habakan/jitsu-in-pico/hardware/kicad/pico2h-carrier/3dprint/pico2h_case.scad

part = "assembly";
// Generated from case_dimensions.json. Units: mm.
module base() { union() {
translate([0,0,0]) linear_extrude(2.4) polygon(points=[[3.477895, 0.034221], [2.964724, 0.136297], [2.469266, 0.304482], [2.0, 0.535898], [1.564954, 0.826587], [1.171573, 1.171573], [0.826587, 1.564954], [0.535898, 2.0], [0.304482, 2.469266], [0.136297, 2.964724], [0.034221, 3.477895], [0.0, 4.0], [0.0, 39.4], [0.034221, 39.922105], [0.136297, 40.435276], [0.304482, 40.930734], [0.535898, 41.4], [0.826587, 41.835046], [1.171573, 42.228427], [1.564954, 42.573413], [2.0, 42.864102], [2.469266, 43.095518], [2.964724, 43.263703], [3.477895, 43.365779], [4.0, 43.4], [59.4, 43.4], [59.922105, 43.365779], [60.435276, 43.263703], [60.930734, 43.095518], [61.4, 42.864102], [61.835046, 42.573413], [62.228427, 42.228427], [62.573413, 41.835046], [62.864102, 41.4], [63.095518, 40.930734], [63.263703, 40.435276], [63.365779, 39.922105], [63.4, 39.4], [63.4, 4.0], [63.365779, 3.477895], [63.263703, 2.964724], [63.095518, 2.469266], [62.864102, 2.0], [62.573413, 1.564954], [62.228427, 1.171573], [61.835046, 0.826587], [61.4, 0.535898], [60.930734, 0.304482], [60.435276, 0.136297], [59.922105, 0.034221], [59.4, 0.0], [4.0, 0.0], [36.873004, 23.124736], [36.643332, 24.279371], [36.264916, 25.394151], [35.744229, 26.45], [35.09018, 27.428853], [34.313961, 28.313961], [33.428853, 29.09018], [32.45, 29.744229], [31.394151, 30.264916], [30.279371, 30.643332], [29.124736, 30.873004], [27.95, 30.95], [26.775264, 30.873004], [25.620629, 30.643332], [24.505849, 30.264916], [23.45, 29.744229], [22.471147, 29.09018], [21.586039, 28.313961], [20.80982, 27.428853], [20.155771, 26.45], [19.635084, 25.394151], [19.256668, 24.279371], [19.026996, 23.124736], [18.95, 21.95], [19.026996, 20.775264], [19.256668, 19.620629], [19.635084, 18.505849], [20.155771, 17.45], [20.80982, 16.471147], [21.586039, 15.586039], [22.471147, 14.80982], [23.45, 14.155771], [24.505849, 13.635084], [25.620629, 13.256668], [26.775264, 13.026996], [27.95, 12.95], [29.124736, 13.026996], [30.279371, 13.256668], [31.394151, 13.635084], [32.45, 14.155771], [33.428853, 14.80982], [34.313961, 15.586039], [35.09018, 16.471147], [35.744229, 17.45], [36.264916, 18.505849], [36.643332, 19.620629], [36.873004, 20.775264], [36.95, 21.95]],paths=[[0, 1, 2, 3, 4, 5, 6, 7, 8, 9, 10, 11, 12, 13, 14, 15, 16, 17, 18, 19, 20, 21, 22, 23, 24, 25, 26, 27, 28, 29, 30, 31, 32, 33, 34, 35, 36, 37, 38, 39, 40, 41, 42, 43, 44, 45, 46, 47, 48, 49, 50, 51], [52, 53, 54, 55, 56, 57, 58, 59, 60, 61, 62, 63, 64, 65, 66, 67, 68, 69, 70, 71, 72, 73, 74, 75, 76, 77, 78, 79, 80, 81, 82, 83, 84, 85, 86, 87, 88, 89, 90, 91, 92, 93, 94, 95, 96, 97, 98, 99]]);
translate([0,0,2.4]) linear_extrude(0.6000000000000001) polygon(points=[[0.034221, 39.922105], [0.136297, 40.435276], [0.304482, 40.930734], [0.535898, 41.4], [0.826587, 41.835046], [1.171573, 42.228427], [1.564954, 42.573413], [2.0, 42.864102], [2.469266, 43.095518], [2.964724, 43.263703], [3.477895, 43.365779], [4.0, 43.4], [59.4, 43.4], [59.922105, 43.365779], [60.435276, 43.263703], [60.930734, 43.095518], [61.4, 42.864102], [61.835046, 42.573413], [62.228427, 42.228427], [62.573413, 41.835046], [62.864102, 41.4], [63.095518, 40.930734], [63.263703, 40.435276], [63.365779, 39.922105], [63.4, 39.4], [63.4, 4.0], [63.365779, 3.477895], [63.263703, 2.964724], [63.095518, 2.469266], [62.864102, 2.0], [62.573413, 1.564954], [62.228427, 1.171573], [61.835046, 0.826587], [61.4, 0.535898], [60.930734, 0.304482], [60.435276, 0.136297], [59.922105, 0.034221], [59.4, 0.0], [4.0, 0.0], [3.477895, 0.034221], [2.964724, 0.136297], [2.469266, 0.304482], [2.0, 0.535898], [1.564954, 0.826587], [1.171573, 1.171573], [0.826587, 1.564954], [0.535898, 2.0], [0.304482, 2.469266], [0.136297, 2.964724], [0.034221, 3.477895], [0.0, 4.0], [0.0, 39.4], [60.817691, 3.9], [60.556072, 3.508459], [60.245584, 3.154416], [59.891541, 2.843928], [59.5, 2.582309], [59.130315, 2.4], [59.4, 2.4], [59.608842, 2.413688], [59.81411, 2.454519], [60.012293, 2.521793], [60.2, 2.614359], [60.374018, 2.730635], [60.531371, 2.868629], [60.669365, 3.025982], [60.785641, 3.2], [60.878207, 3.387707], [60.945481, 3.58589], [60.986312, 3.791158], [61.0, 4.0], [61.0, 4.269685], [59.608842, 40.986312], [59.4, 41.0], [59.130315, 41.0], [59.5, 40.817691], [59.891541, 40.556072], [60.245584, 40.245584], [60.556072, 39.891541], [60.817691, 39.5], [61.0, 39.130315], [61.0, 39.4], [60.986312, 39.608842], [60.945481, 39.81411], [60.878207, 40.012293], [60.785641, 40.2], [60.669365, 40.374018], [60.531371, 40.531371], [60.374018, 40.669365], [60.2, 40.785641], [60.012293, 40.878207], [59.81411, 40.945481], [9.3, 37.7], [9.269202, 37.230106], [9.177333, 36.768251], [9.025966, 36.32234], [8.817691, 35.9], [8.556072, 35.508459], [8.245584, 35.154416], [7.891541, 34.843928], [7.5, 34.582309], [7.07766, 34.374034], [6.631749, 34.222667], [6.169894, 34.130798], [5.7, 34.1], [5.230106, 34.130798], [4.768251, 34.222667], [4.32234, 34.374034], [3.9, 34.582309], [3.508459, 34.843928], [3.154416, 35.154416], [2.843928, 35.508459], [2.582309, 35.9], [2.4, 36.269685], [2.4, 7.130315], [2.582309, 7.5], [2.843928, 7.891541], [3.154416, 8.245584], [3.508459, 8.556072], [3.9, 8.817691], [4.32234, 9.025966], [4.768251, 9.177333], [5.230106, 9.269202], [5.7, 9.3], [6.169894, 9.269202], [6.631749, 9.177333], [7.07766, 9.025966], [7.5, 8.817691], [7.891541, 8.556072], [8.245584, 8.245584], [8.556072, 7.891541], [8.817691, 7.5], [9.025966, 7.07766], [9.177333, 6.631749], [9.269202, 6.169894], [9.3, 5.7], [9.269202, 5.230106], [9.177333, 4.768251], [9.025966, 4.32234], [8.817691, 3.9], [8.556072, 3.508459], [8.245584, 3.154416], [7.891541, 2.843928], [7.5, 2.582309], [7.130315, 2.4], [56.269685, 2.4], [55.9, 2.582309], [55.508459, 2.843928], [55.154416, 3.154416], [54.843928, 3.508459], [54.582309, 3.9], [54.374034, 4.32234], [54.222667, 4.768251], [54.130798, 5.230106], [54.1, 5.7], [54.130798, 6.169894], [54.222667, 6.631749], [54.374034, 7.07766], [54.582309, 7.5], [54.843928, 7.891541], [55.154416, 8.245584], [55.508459, 8.556072], [55.9, 8.817691], [56.32234, 9.025966], [56.768251, 9.177333], [57.230106, 9.269202], [57.7, 9.3], [58.169894, 9.269202], [58.631749, 9.177333], [59.07766, 9.025966], [59.5, 8.817691], [59.891541, 8.556072], [60.245584, 8.245584], [60.556072, 7.891541], [60.817691, 7.5], [61.0, 7.130315], [61.0, 36.269685], [60.817691, 35.9], [60.556072, 35.508459], [60.245584, 35.154416], [59.891541, 34.843928], [59.5, 34.582309], [59.07766, 34.374034], [58.631749, 34.222667], [58.169894, 34.130798], [57.7, 34.1], [57.230106, 34.130798], [56.768251, 34.222667], [56.32234, 34.374034], [55.9, 34.582309], [55.508459, 34.843928], [55.154416, 35.154416], [54.843928, 35.508459], [54.582309, 35.9], [54.374034, 36.32234], [54.222667, 36.768251], [54.130798, 37.230106], [54.1, 37.7], [54.130798, 38.169894], [54.222667, 38.631749], [54.374034, 39.07766], [54.582309, 39.5], [54.843928, 39.891541], [55.154416, 40.245584], [55.508459, 40.556072], [55.9, 40.817691], [56.269685, 41.0], [7.130315, 41.0], [7.5, 40.817691], [7.891541, 40.556072], [8.245584, 40.245584], [8.556072, 39.891541], [8.817691, 39.5], [9.025966, 39.07766], [9.177333, 38.631749], [9.269202, 38.169894], [2.454519, 39.81411], [2.413688, 39.608842], [2.4, 39.4], [2.4, 39.130315], [2.582309, 39.5], [2.843928, 39.891541], [3.154416, 40.245584], [3.508459, 40.556072], [3.9, 40.817691], [4.269685, 41.0], [4.0, 41.0], [3.791158, 40.986312], [3.58589, 40.945481], [3.387707, 40.878207], [3.2, 40.785641], [3.025982, 40.669365], [2.868629, 40.531371], [2.730635, 40.374018], [2.614359, 40.2], [2.521793, 40.012293], [4.0, 2.4], [4.269685, 2.4], [3.9, 2.582309], [3.508459, 2.843928], [3.154416, 3.154416], [2.843928, 3.508459], [2.582309, 3.9], [2.4, 4.269685], [2.4, 4.0], [2.413688, 3.791158], [2.454519, 3.58589], [2.521793, 3.387707], [2.614359, 3.2], [2.730635, 3.025982], [2.868629, 2.868629], [3.025982, 2.730635], [3.2, 2.614359], [3.387707, 2.521793], [3.58589, 2.454519], [3.791158, 2.413688]],paths=[[0, 1, 2, 3, 4, 5, 6, 7, 8, 9, 10, 11, 12, 13, 14, 15, 16, 17, 18, 19, 20, 21, 22, 23, 24, 25, 26, 27, 28, 29, 30, 31, 32, 33, 34, 35, 36, 37, 38, 39, 40, 41, 42, 43, 44, 45, 46, 47, 48, 49, 50, 51], [52, 53, 54, 55, 56, 57, 58, 59, 60, 61, 62, 63, 64, 65, 66, 67, 68, 69, 70, 71], [72, 73, 74, 75, 76, 77, 78, 79, 80, 81, 82, 83, 84, 85, 86, 87, 88, 89, 90, 91], [92, 93, 94, 95, 96, 97, 98, 99, 100, 101, 102, 103, 104, 105, 106, 107, 108, 109, 110, 111, 112, 113, 114, 115, 116, 117, 118, 119, 120, 121, 122, 123, 124, 125, 126, 127, 128, 129, 130, 131, 132, 133, 134, 135, 136, 137, 138, 139, 140, 141, 142, 143, 144, 145, 146, 147, 148, 149, 150, 151, 152, 153, 154, 155, 156, 157, 158, 159, 160, 161, 162, 163, 164, 165, 166, 167, 168, 169, 170, 171, 172, 173, 174, 175, 176, 177, 178, 179, 180, 181, 182, 183, 184, 185, 186, 187, 188, 189, 190, 191, 192, 193, 194, 195, 196, 197, 198, 199, 200, 201, 202, 203, 204, 205, 206, 207, 208, 209, 210, 211, 212, 213, 214, 215], [216, 217, 218, 219, 220, 221, 222, 223, 224, 225, 226, 227, 228, 229, 230, 231, 232, 233, 234, 235], [236, 237, 238, 239, 240, 241, 242, 243, 244, 245, 246, 247, 248, 249, 250, 251, 252, 253, 254, 255]]);
translate([0,0,2.4]) linear_extrude(0.6000000000000001) polygon(points=[[10.8, 12.794744], [10.541904, 12.667465], [10.269402, 12.574963], [9.987158, 12.518821], [9.7, 12.5], [9.412842, 12.518821], [9.130598, 12.574963], [8.858096, 12.667465], [8.6, 12.794744], [8.360725, 12.954623], [8.144365, 13.144365], [7.954623, 13.360725], [7.794744, 13.6], [7.667465, 13.858096], [7.574963, 14.130598], [7.518821, 14.412842], [7.5, 14.7], [7.518821, 14.987158], [7.574963, 15.269402], [7.667465, 15.541904], [7.794744, 15.8], [7.954623, 16.039275], [8.144365, 16.255635], [8.360725, 16.445377], [8.6, 16.605256], [8.858096, 16.732535], [9.130598, 16.825037], [9.412842, 16.881179], [9.7, 16.9], [9.987158, 16.881179], [10.269402, 16.825037], [10.541904, 16.732535], [10.8, 16.605256], [11.039275, 16.445377], [11.255635, 16.255635], [11.445377, 16.039275], [11.605256, 15.8], [11.732535, 15.541904], [11.825037, 15.269402], [11.881179, 14.987158], [11.9, 14.7], [11.881179, 14.412842], [11.825037, 14.130598], [11.732535, 13.858096], [11.605256, 13.6], [11.445377, 13.360725], [11.255635, 13.144365], [11.039275, 12.954623]],paths=[[0, 1, 2, 3, 4, 5, 6, 7, 8, 9, 10, 11, 12, 13, 14, 15, 16, 17, 18, 19, 20, 21, 22, 23, 24, 25, 26, 27, 28, 29, 30, 31, 32, 33, 34, 35, 36, 37, 38, 39, 40, 41, 42, 43, 44, 45, 46, 47]]);
translate([0,0,2.4]) linear_extrude(0.6000000000000001) polygon(points=[[11.039275, 27.454623], [10.8, 27.294744], [10.541904, 27.167465], [10.269402, 27.074963], [9.987158, 27.018821], [9.7, 27.0], [9.412842, 27.018821], [9.130598, 27.074963], [8.858096, 27.167465], [8.6, 27.294744], [8.360725, 27.454623], [8.144365, 27.644365], [7.954623, 27.860725], [7.794744, 28.1], [7.667465, 28.358096], [7.574963, 28.630598], [7.518821, 28.912842], [7.5, 29.2], [7.518821, 29.487158], [7.574963, 29.769402], [7.667465, 30.041904], [7.794744, 30.3], [7.954623, 30.539275], [8.144365, 30.755635], [8.360725, 30.945377], [8.6, 31.105256], [8.858096, 31.232535], [9.130598, 31.325037], [9.412842, 31.381179], [9.7, 31.4], [9.987158, 31.381179], [10.269402, 31.325037], [10.541904, 31.232535], [10.8, 31.105256], [11.039275, 30.945377], [11.255635, 30.755635], [11.445377, 30.539275], [11.605256, 30.3], [11.732535, 30.041904], [11.825037, 29.769402], [11.881179, 29.487158], [11.9, 29.2], [11.881179, 28.912842], [11.825037, 28.630598], [11.732535, 28.358096], [11.605256, 28.1], [11.445377, 27.860725], [11.255635, 27.644365]],paths=[[0, 1, 2, 3, 4, 5, 6, 7, 8, 9, 10, 11, 12, 13, 14, 15, 16, 17, 18, 19, 20, 21, 22, 23, 24, 25, 26, 27, 28, 29, 30, 31, 32, 33, 34, 35, 36, 37, 38, 39, 40, 41, 42, 43, 44, 45, 46, 47]]);
translate([0,0,2.4]) linear_extrude(0.6000000000000001) polygon(points=[[47.755635, 13.144365], [47.539275, 12.954623], [47.3, 12.794744], [47.041904, 12.667465], [46.769402, 12.574963], [46.487158, 12.518821], [46.2, 12.5], [45.912842, 12.518821], [45.630598, 12.574963], [45.358096, 12.667465], [45.1, 12.794744], [44.860725, 12.954623], [44.644365, 13.144365], [44.454623, 13.360725], [44.294744, 13.6], [44.167465, 13.858096], [44.074963, 14.130598], [44.018821, 14.412842], [44.0, 14.7], [44.018821, 14.987158], [44.074963, 15.269402], [44.167465, 15.541904], [44.294744, 15.8], [44.454623, 16.039275], [44.644365, 16.255635], [44.860725, 16.445377], [45.1, 16.605256], [45.358096, 16.732535], [45.630598, 16.825037], [45.912842, 16.881179], [46.2, 16.9], [46.487158, 16.881179], [46.769402, 16.825037], [47.041904, 16.732535], [47.3, 16.605256], [47.539275, 16.445377], [47.755635, 16.255635], [47.945377, 16.039275], [48.105256, 15.8], [48.232535, 15.541904], [48.325037, 15.269402], [48.381179, 14.987158], [48.4, 14.7], [48.381179, 14.412842], [48.325037, 14.130598], [48.232535, 13.858096], [48.105256, 13.6], [47.945377, 13.360725]],paths=[[0, 1, 2, 3, 4, 5, 6, 7, 8, 9, 10, 11, 12, 13, 14, 15, 16, 17, 18, 19, 20, 21, 22, 23, 24, 25, 26, 27, 28, 29, 30, 31, 32, 33, 34, 35, 36, 37, 38, 39, 40, 41, 42, 43, 44, 45, 46, 47]]);
translate([0,0,2.4]) linear_extrude(0.6000000000000001) polygon(points=[[47.945377, 27.860725], [47.755635, 27.644365], [47.539275, 27.454623], [47.3, 27.294744], [47.041904, 27.167465], [46.769402, 27.074963], [46.487158, 27.018821], [46.2, 27.0], [45.912842, 27.018821], [45.630598, 27.074963], [45.358096, 27.167465], [45.1, 27.294744], [44.860725, 27.454623], [44.644365, 27.644365], [44.454623, 27.860725], [44.294744, 28.1], [44.167465, 28.358096], [44.074963, 28.630598], [44.018821, 28.912842], [44.0, 29.2], [44.018821, 29.487158], [44.074963, 29.769402], [44.167465, 30.041904], [44.294744, 30.3], [44.454623, 30.539275], [44.644365, 30.755635], [44.860725, 30.945377], [45.1, 31.105256], [45.358096, 31.232535], [45.630598, 31.325037], [45.912842, 31.381179], [46.2, 31.4], [46.487158, 31.381179], [46.769402, 31.325037], [47.041904, 31.232535], [47.3, 31.105256], [47.539275, 30.945377], [47.755635, 30.755635], [47.945377, 30.539275], [48.105256, 30.3], [48.232535, 30.041904], [48.325037, 29.769402], [48.381179, 29.487158], [48.4, 29.2], [48.381179, 28.912842], [48.325037, 28.630598], [48.232535, 28.358096], [48.105256, 28.1]],paths=[[0, 1, 2, 3, 4, 5, 6, 7, 8, 9, 10, 11, 12, 13, 14, 15, 16, 17, 18, 19, 20, 21, 22, 23, 24, 25, 26, 27, 28, 29, 30, 31, 32, 33, 34, 35, 36, 37, 38, 39, 40, 41, 42, 43, 44, 45, 46, 47]]);
translate([0,0,2.4]) linear_extrude(0.6000000000000001) polygon(points=[[13.9, 6.7], [12.7, 6.7], [12.7, 7.9], [13.9, 7.9]],paths=[[0, 1, 2, 3]]);
translate([0,0,2.4]) linear_extrude(0.6000000000000001) polygon(points=[[13.9, 37.2], [13.9, 36.0], [12.7, 36.0], [12.7, 37.2]],paths=[[0, 1, 2, 3]]);
translate([0,0,2.4]) linear_extrude(0.6000000000000001) polygon(points=[[42.0, 7.9], [43.2, 7.9], [43.2, 6.7], [42.0, 6.7]],paths=[[0, 1, 2, 3]]);
translate([0,0,2.4]) linear_extrude(0.6000000000000001) polygon(points=[[42.0, 36.0], [42.0, 37.2], [43.2, 37.2], [43.2, 36.0]],paths=[[0, 1, 2, 3]]);
translate([0,0,3.0]) linear_extrude(0.3999999999999999) polygon(points=[[0.826587, 41.835046], [1.171573, 42.228427], [1.564954, 42.573413], [2.0, 42.864102], [2.469266, 43.095518], [2.964724, 43.263703], [3.477895, 43.365779], [4.0, 43.4], [59.4, 43.4], [59.922105, 43.365779], [60.435276, 43.263703], [60.930734, 43.095518], [61.4, 42.864102], [61.835046, 42.573413], [62.228427, 42.228427], [62.573413, 41.835046], [62.864102, 41.4], [63.095518, 40.930734], [63.263703, 40.435276], [63.365779, 39.922105], [63.4, 39.4], [63.4, 4.0], [63.365779, 3.477895], [63.263703, 2.964724], [63.095518, 2.469266], [62.864102, 2.0], [62.573413, 1.564954], [62.228427, 1.171573], [61.835046, 0.826587], [61.4, 0.535898], [60.930734, 0.304482], [60.435276, 0.136297], [59.922105, 0.034221], [59.4, 0.0], [4.0, 0.0], [3.477895, 0.034221], [2.964724, 0.136297], [2.469266, 0.304482], [2.0, 0.535898], [1.564954, 0.826587], [1.171573, 1.171573], [0.826587, 1.564954], [0.535898, 2.0], [0.304482, 2.469266], [0.136297, 2.964724], [0.034221, 3.477895], [0.0, 4.0], [0.0, 39.4], [0.034221, 39.922105], [0.136297, 40.435276], [0.304482, 40.930734], [0.535898, 41.4], [59.5, 2.582309], [59.130315, 2.4], [59.4, 2.4], [59.608842, 2.413688], [59.81411, 2.454519], [60.012293, 2.521793], [60.2, 2.614359], [60.374018, 2.730635], [60.531371, 2.868629], [60.669365, 3.025982], [60.785641, 3.2], [60.878207, 3.387707], [60.945481, 3.58589], [60.986312, 3.791158], [61.0, 4.0], [61.0, 4.269685], [60.817691, 3.9], [60.556072, 3.508459], [60.245584, 3.154416], [59.891541, 2.843928], [59.891541, 40.556072], [60.245584, 40.245584], [60.556072, 39.891541], [60.817691, 39.5], [61.0, 39.130315], [61.0, 39.4], [60.986312, 39.608842], [60.945481, 39.81411], [60.878207, 40.012293], [60.785641, 40.2], [60.669365, 40.374018], [60.531371, 40.531371], [60.374018, 40.669365], [60.2, 40.785641], [60.012293, 40.878207], [59.81411, 40.945481], [59.608842, 40.986312], [59.4, 41.0], [59.130315, 41.0], [59.5, 40.817691], [8.817691, 35.9], [8.556072, 35.508459], [8.245584, 35.154416], [7.891541, 34.843928], [7.5, 34.582309], [7.07766, 34.374034], [6.631749, 34.222667], [6.169894, 34.130798], [5.7, 34.1], [5.230106, 34.130798], [4.768251, 34.222667], [4.32234, 34.374034], [3.9, 34.582309], [3.508459, 34.843928], [3.154416, 35.154416], [2.843928, 35.508459], [2.582309, 35.9], [2.4, 36.269685], [2.4, 7.130315], [2.582309, 7.5], [2.843928, 7.891541], [3.154416, 8.245584], [3.508459, 8.556072], [3.9, 8.817691], [4.32234, 9.025966], [4.768251, 9.177333], [5.230106, 9.269202], [5.7, 9.3], [6.169894, 9.269202], [6.631749, 9.177333], [7.07766, 9.025966], [7.5, 8.817691], [7.891541, 8.556072], [8.245584, 8.245584], [8.556072, 7.891541], [8.817691, 7.5], [9.025966, 7.07766], [9.177333, 6.631749], [9.269202, 6.169894], [9.3, 5.7], [9.269202, 5.230106], [9.177333, 4.768251], [9.025966, 4.32234], [8.817691, 3.9], [8.556072, 3.508459], [8.245584, 3.154416], [7.891541, 2.843928], [7.5, 2.582309], [7.130315, 2.4], [56.269685, 2.4], [55.9, 2.582309], [55.508459, 2.843928], [55.154416, 3.154416], [54.843928, 3.508459], [54.582309, 3.9], [54.374034, 4.32234], [54.222667, 4.768251], [54.130798, 5.230106], [54.1, 5.7], [54.130798, 6.169894], [54.222667, 6.631749], [54.374034, 7.07766], [54.582309, 7.5], [54.843928, 7.891541], [55.154416, 8.245584], [55.508459, 8.556072], [55.9, 8.817691], [56.32234, 9.025966], [56.768251, 9.177333], [57.230106, 9.269202], [57.7, 9.3], [58.169894, 9.269202], [58.631749, 9.177333], [59.07766, 9.025966], [59.5, 8.817691], [59.891541, 8.556072], [60.245584, 8.245584], [60.556072, 7.891541], [60.817691, 7.5], [61.0, 7.130315], [61.0, 36.269685], [60.817691, 35.9], [60.556072, 35.508459], [60.245584, 35.154416], [59.891541, 34.843928], [59.5, 34.582309], [59.07766, 34.374034], [58.631749, 34.222667], [58.169894, 34.130798], [57.7, 34.1], [57.230106, 34.130798], [56.768251, 34.222667], [56.32234, 34.374034], [55.9, 34.582309], [55.508459, 34.843928], [55.154416, 35.154416], [54.843928, 35.508459], [54.582309, 35.9], [54.374034, 36.32234], [54.222667, 36.768251], [54.130798, 37.230106], [54.1, 37.7], [54.130798, 38.169894], [54.222667, 38.631749], [54.374034, 39.07766], [54.582309, 39.5], [54.843928, 39.891541], [55.154416, 40.245584], [55.508459, 40.556072], [55.9, 40.817691], [56.269685, 41.0], [7.130315, 41.0], [7.5, 40.817691], [7.891541, 40.556072], [8.245584, 40.245584], [8.556072, 39.891541], [8.817691, 39.5], [9.025966, 39.07766], [9.177333, 38.631749], [9.269202, 38.169894], [9.3, 37.7], [9.269202, 37.230106], [9.177333, 36.768251], [9.025966, 36.32234], [2.582309, 39.5], [2.843928, 39.891541], [3.154416, 40.245584], [3.508459, 40.556072], [3.9, 40.817691], [4.269685, 41.0], [4.0, 41.0], [3.791158, 40.986312], [3.58589, 40.945481], [3.387707, 40.878207], [3.2, 40.785641], [3.025982, 40.669365], [2.868629, 40.531371], [2.730635, 40.374018], [2.614359, 40.2], [2.521793, 40.012293], [2.454519, 39.81411], [2.413688, 39.608842], [2.4, 39.4], [2.4, 39.130315], [3.154416, 3.154416], [2.843928, 3.508459], [2.582309, 3.9], [2.4, 4.269685], [2.4, 4.0], [2.413688, 3.791158], [2.454519, 3.58589], [2.521793, 3.387707], [2.614359, 3.2], [2.730635, 3.025982], [2.868629, 2.868629], [3.025982, 2.730635], [3.2, 2.614359], [3.387707, 2.521793], [3.58589, 2.454519], [3.791158, 2.413688], [4.0, 2.4], [4.269685, 2.4], [3.9, 2.582309], [3.508459, 2.843928]],paths=[[0, 1, 2, 3, 4, 5, 6, 7, 8, 9, 10, 11, 12, 13, 14, 15, 16, 17, 18, 19, 20, 21, 22, 23, 24, 25, 26, 27, 28, 29, 30, 31, 32, 33, 34, 35, 36, 37, 38, 39, 40, 41, 42, 43, 44, 45, 46, 47, 48, 49, 50, 51], [52, 53, 54, 55, 56, 57, 58, 59, 60, 61, 62, 63, 64, 65, 66, 67, 68, 69, 70, 71], [72, 73, 74, 75, 76, 77, 78, 79, 80, 81, 82, 83, 84, 85, 86, 87, 88, 89, 90, 91], [92, 93, 94, 95, 96, 97, 98, 99, 100, 101, 102, 103, 104, 105, 106, 107, 108, 109, 110, 111, 112, 113, 114, 115, 116, 117, 118, 119, 120, 121, 122, 123, 124, 125, 126, 127, 128, 129, 130, 131, 132, 133, 134, 135, 136, 137, 138, 139, 140, 141, 142, 143, 144, 145, 146, 147, 148, 149, 150, 151, 152, 153, 154, 155, 156, 157, 158, 159, 160, 161, 162, 163, 164, 165, 166, 167, 168, 169, 170, 171, 172, 173, 174, 175, 176, 177, 178, 179, 180, 181, 182, 183, 184, 185, 186, 187, 188, 189, 190, 191, 192, 193, 194, 195, 196, 197, 198, 199, 200, 201, 202, 203, 204, 205, 206, 207, 208, 209, 210, 211, 212, 213, 214, 215], [216, 217, 218, 219, 220, 221, 222, 223, 224, 225, 226, 227, 228, 229, 230, 231, 232, 233, 234, 235], [236, 237, 238, 239, 240, 241, 242, 243, 244, 245, 246, 247, 248, 249, 250, 251, 252, 253, 254, 255]]);
translate([0,0,3.0]) linear_extrude(0.3999999999999999) polygon(points=[[9.7, 12.5], [9.412842, 12.518821], [9.130598, 12.574963], [8.858096, 12.667465], [8.6, 12.794744], [8.360725, 12.954623], [8.144365, 13.144365], [7.954623, 13.360725], [7.794744, 13.6], [7.667465, 13.858096], [7.574963, 14.130598], [7.518821, 14.412842], [7.5, 14.7], [7.518821, 14.987158], [7.574963, 15.269402], [7.667465, 15.541904], [7.794744, 15.8], [7.954623, 16.039275], [8.144365, 16.255635], [8.360725, 16.445377], [8.6, 16.605256], [8.858096, 16.732535], [9.130598, 16.825037], [9.412842, 16.881179], [9.7, 16.9], [9.987158, 16.881179], [10.269402, 16.825037], [10.541904, 16.732535], [10.8, 16.605256], [11.039275, 16.445377], [11.255635, 16.255635], [11.445377, 16.039275], [11.605256, 15.8], [11.732535, 15.541904], [11.825037, 15.269402], [11.881179, 14.987158], [11.9, 14.7], [11.881179, 14.412842], [11.825037, 14.130598], [11.732535, 13.858096], [11.605256, 13.6], [11.445377, 13.360725], [11.255635, 13.144365], [11.039275, 12.954623], [10.8, 12.794744], [10.541904, 12.667465], [10.269402, 12.574963], [9.987158, 12.518821], [9.804421, 15.493156], [9.7, 15.5], [9.595579, 15.493156], [9.492945, 15.472741], [9.393853, 15.439104], [9.3, 15.39282], [9.212991, 15.334683], [9.134315, 15.265685], [9.065317, 15.187009], [9.00718, 15.1], [8.960896, 15.006147], [8.927259, 14.907055], [8.906844, 14.804421], [8.9, 14.7], [8.906844, 14.595579], [8.927259, 14.492945], [8.960896, 14.393853], [9.00718, 14.3], [9.065317, 14.212991], [9.134315, 14.134315], [9.212991, 14.065317], [9.3, 14.00718], [9.393853, 13.960896], [9.492945, 13.927259], [9.595579, 13.906844], [9.7, 13.9], [9.804421, 13.906844], [9.907055, 13.927259], [10.006147, 13.960896], [10.1, 14.00718], [10.187009, 14.065317], [10.265685, 14.134315], [10.334683, 14.212991], [10.39282, 14.3], [10.439104, 14.393853], [10.472741, 14.492945], [10.493156, 14.595579], [10.5, 14.7], [10.493156, 14.804421], [10.472741, 14.907055], [10.439104, 15.006147], [10.39282, 15.1], [10.334683, 15.187009], [10.265685, 15.265685], [10.187009, 15.334683], [10.1, 15.39282], [10.006147, 15.439104], [9.907055, 15.472741]],paths=[[0, 1, 2, 3, 4, 5, 6, 7, 8, 9, 10, 11, 12, 13, 14, 15, 16, 17, 18, 19, 20, 21, 22, 23, 24, 25, 26, 27, 28, 29, 30, 31, 32, 33, 34, 35, 36, 37, 38, 39, 40, 41, 42, 43, 44, 45, 46, 47], [48, 49, 50, 51, 52, 53, 54, 55, 56, 57, 58, 59, 60, 61, 62, 63, 64, 65, 66, 67, 68, 69, 70, 71, 72, 73, 74, 75, 76, 77, 78, 79, 80, 81, 82, 83, 84, 85, 86, 87, 88, 89, 90, 91, 92, 93, 94, 95]]);
translate([0,0,3.0]) linear_extrude(0.3999999999999999) polygon(points=[[10.269402, 27.074963], [9.987158, 27.018821], [9.7, 27.0], [9.412842, 27.018821], [9.130598, 27.074963], [8.858096, 27.167465], [8.6, 27.294744], [8.360725, 27.454623], [8.144365, 27.644365], [7.954623, 27.860725], [7.794744, 28.1], [7.667465, 28.358096], [7.574963, 28.630598], [7.518821, 28.912842], [7.5, 29.2], [7.518821, 29.487158], [7.574963, 29.769402], [7.667465, 30.041904], [7.794744, 30.3], [7.954623, 30.539275], [8.144365, 30.755635], [8.360725, 30.945377], [8.6, 31.105256], [8.858096, 31.232535], [9.130598, 31.325037], [9.412842, 31.381179], [9.7, 31.4], [9.987158, 31.381179], [10.269402, 31.325037], [10.541904, 31.232535], [10.8, 31.105256], [11.039275, 30.945377], [11.255635, 30.755635], [11.445377, 30.539275], [11.605256, 30.3], [11.732535, 30.041904], [11.825037, 29.769402], [11.881179, 29.487158], [11.9, 29.2], [11.881179, 28.912842], [11.825037, 28.630598], [11.732535, 28.358096], [11.605256, 28.1], [11.445377, 27.860725], [11.255635, 27.644365], [11.039275, 27.454623], [10.8, 27.294744], [10.541904, 27.167465], [10.006147, 29.939104], [9.907055, 29.972741], [9.804421, 29.993156], [9.7, 30.0], [9.595579, 29.993156], [9.492945, 29.972741], [9.393853, 29.939104], [9.3, 29.89282], [9.212991, 29.834683], [9.134315, 29.765685], [9.065317, 29.687009], [9.00718, 29.6], [8.960896, 29.506147], [8.927259, 29.407055], [8.906844, 29.304421], [8.9, 29.2], [8.906844, 29.095579], [8.927259, 28.992945], [8.960896, 28.893853], [9.00718, 28.8], [9.065317, 28.712991], [9.134315, 28.634315], [9.212991, 28.565317], [9.3, 28.50718], [9.393853, 28.460896], [9.492945, 28.427259], [9.595579, 28.406844], [9.7, 28.4], [9.804421, 28.406844], [9.907055, 28.427259], [10.006147, 28.460896], [10.1, 28.50718], [10.187009, 28.565317], [10.265685, 28.634315], [10.334683, 28.712991], [10.39282, 28.8], [10.439104, 28.893853], [10.472741, 28.992945], [10.493156, 29.095579], [10.5, 29.2], [10.493156, 29.304421], [10.472741, 29.407055], [10.439104, 29.506147], [10.39282, 29.6], [10.334683, 29.687009], [10.265685, 29.765685], [10.187009, 29.834683], [10.1, 29.89282]],paths=[[0, 1, 2, 3, 4, 5, 6, 7, 8, 9, 10, 11, 12, 13, 14, 15, 16, 17, 18, 19, 20, 21, 22, 23, 24, 25, 26, 27, 28, 29, 30, 31, 32, 33, 34, 35, 36, 37, 38, 39, 40, 41, 42, 43, 44, 45, 46, 47], [48, 49, 50, 51, 52, 53, 54, 55, 56, 57, 58, 59, 60, 61, 62, 63, 64, 65, 66, 67, 68, 69, 70, 71, 72, 73, 74, 75, 76, 77, 78, 79, 80, 81, 82, 83, 84, 85, 86, 87, 88, 89, 90, 91, 92, 93, 94, 95]]);
translate([0,0,3.0]) linear_extrude(0.3999999999999999) polygon(points=[[47.3, 12.794744], [47.041904, 12.667465], [46.769402, 12.574963], [46.487158, 12.518821], [46.2, 12.5], [45.912842, 12.518821], [45.630598, 12.574963], [45.358096, 12.667465], [45.1, 12.794744], [44.860725, 12.954623], [44.644365, 13.144365], [44.454623, 13.360725], [44.294744, 13.6], [44.167465, 13.858096], [44.074963, 14.130598], [44.018821, 14.412842], [44.0, 14.7], [44.018821, 14.987158], [44.074963, 15.269402], [44.167465, 15.541904], [44.294744, 15.8], [44.454623, 16.039275], [44.644365, 16.255635], [44.860725, 16.445377], [45.1, 16.605256], [45.358096, 16.732535], [45.630598, 16.825037], [45.912842, 16.881179], [46.2, 16.9], [46.487158, 16.881179], [46.769402, 16.825037], [47.041904, 16.732535], [47.3, 16.605256], [47.539275, 16.445377], [47.755635, 16.255635], [47.945377, 16.039275], [48.105256, 15.8], [48.232535, 15.541904], [48.325037, 15.269402], [48.381179, 14.987158], [48.4, 14.7], [48.381179, 14.412842], [48.325037, 14.130598], [48.232535, 13.858096], [48.105256, 13.6], [47.945377, 13.360725], [47.755635, 13.144365], [47.539275, 12.954623], [46.687009, 15.334683], [46.6, 15.39282], [46.506147, 15.439104], [46.407055, 15.472741], [46.304421, 15.493156], [46.2, 15.5], [46.095579, 15.493156], [45.992945, 15.472741], [45.893853, 15.439104], [45.8, 15.39282], [45.712991, 15.334683], [45.634315, 15.265685], [45.565317, 15.187009], [45.50718, 15.1], [45.460896, 15.006147], [45.427259, 14.907055], [45.406844, 14.804421], [45.4, 14.7], [45.406844, 14.595579], [45.427259, 14.492945], [45.460896, 14.393853], [45.50718, 14.3], [45.565317, 14.212991], [45.634315, 14.134315], [45.712991, 14.065317], [45.8, 14.00718], [45.893853, 13.960896], [45.992945, 13.927259], [46.095579, 13.906844], [46.2, 13.9], [46.304421, 13.906844], [46.407055, 13.927259], [46.506147, 13.960896], [46.6, 14.00718], [46.687009, 14.065317], [46.765685, 14.134315], [46.834683, 14.212991], [46.89282, 14.3], [46.939104, 14.393853], [46.972741, 14.492945], [46.993156, 14.595579], [47.0, 14.7], [46.993156, 14.804421], [46.972741, 14.907055], [46.939104, 15.006147], [46.89282, 15.1], [46.834683, 15.187009], [46.765685, 15.265685]],paths=[[0, 1, 2, 3, 4, 5, 6, 7, 8, 9, 10, 11, 12, 13, 14, 15, 16, 17, 18, 19, 20, 21, 22, 23, 24, 25, 26, 27, 28, 29, 30, 31, 32, 33, 34, 35, 36, 37, 38, 39, 40, 41, 42, 43, 44, 45, 46, 47], [48, 49, 50, 51, 52, 53, 54, 55, 56, 57, 58, 59, 60, 61, 62, 63, 64, 65, 66, 67, 68, 69, 70, 71, 72, 73, 74, 75, 76, 77, 78, 79, 80, 81, 82, 83, 84, 85, 86, 87, 88, 89, 90, 91, 92, 93, 94, 95]]);
translate([0,0,3.0]) linear_extrude(0.3999999999999999) polygon(points=[[47.755635, 27.644365], [47.539275, 27.454623], [47.3, 27.294744], [47.041904, 27.167465], [46.769402, 27.074963], [46.487158, 27.018821], [46.2, 27.0], [45.912842, 27.018821], [45.630598, 27.074963], [45.358096, 27.167465], [45.1, 27.294744], [44.860725, 27.454623], [44.644365, 27.644365], [44.454623, 27.860725], [44.294744, 28.1], [44.167465, 28.358096], [44.074963, 28.630598], [44.018821, 28.912842], [44.0, 29.2], [44.018821, 29.487158], [44.074963, 29.769402], [44.167465, 30.041904], [44.294744, 30.3], [44.454623, 30.539275], [44.644365, 30.755635], [44.860725, 30.945377], [45.1, 31.105256], [45.358096, 31.232535], [45.630598, 31.325037], [45.912842, 31.381179], [46.2, 31.4], [46.487158, 31.381179], [46.769402, 31.325037], [47.041904, 31.232535], [47.3, 31.105256], [47.539275, 30.945377], [47.755635, 30.755635], [47.945377, 30.539275], [48.105256, 30.3], [48.232535, 30.041904], [48.325037, 29.769402], [48.381179, 29.487158], [48.4, 29.2], [48.381179, 28.912842], [48.325037, 28.630598], [48.232535, 28.358096], [48.105256, 28.1], [47.945377, 27.860725], [46.834683, 29.687009], [46.765685, 29.765685], [46.687009, 29.834683], [46.6, 29.89282], [46.506147, 29.939104], [46.407055, 29.972741], [46.304421, 29.993156], [46.2, 30.0], [46.095579, 29.993156], [45.992945, 29.972741], [45.893853, 29.939104], [45.8, 29.89282], [45.712991, 29.834683], [45.634315, 29.765685], [45.565317, 29.687009], [45.50718, 29.6], [45.460896, 29.506147], [45.427259, 29.407055], [45.406844, 29.304421], [45.4, 29.2], [45.406844, 29.095579], [45.427259, 28.992945], [45.460896, 28.893853], [45.50718, 28.8], [45.565317, 28.712991], [45.634315, 28.634315], [45.712991, 28.565317], [45.8, 28.50718], [45.893853, 28.460896], [45.992945, 28.427259], [46.095579, 28.406844], [46.2, 28.4], [46.304421, 28.406844], [46.407055, 28.427259], [46.506147, 28.460896], [46.6, 28.50718], [46.687009, 28.565317], [46.765685, 28.634315], [46.834683, 28.712991], [46.89282, 28.8], [46.939104, 28.893853], [46.972741, 28.992945], [46.993156, 29.095579], [47.0, 29.2], [46.993156, 29.304421], [46.972741, 29.407055], [46.939104, 29.506147], [46.89282, 29.6]],paths=[[0, 1, 2, 3, 4, 5, 6, 7, 8, 9, 10, 11, 12, 13, 14, 15, 16, 17, 18, 19, 20, 21, 22, 23, 24, 25, 26, 27, 28, 29, 30, 31, 32, 33, 34, 35, 36, 37, 38, 39, 40, 41, 42, 43, 44, 45, 46, 47], [48, 49, 50, 51, 52, 53, 54, 55, 56, 57, 58, 59, 60, 61, 62, 63, 64, 65, 66, 67, 68, 69, 70, 71, 72, 73, 74, 75, 76, 77, 78, 79, 80, 81, 82, 83, 84, 85, 86, 87, 88, 89, 90, 91, 92, 93, 94, 95]]);
translate([0,0,3.0]) linear_extrude(0.3999999999999999) polygon(points=[[13.9, 6.7], [12.7, 6.7], [12.7, 7.9], [13.9, 7.9]],paths=[[0, 1, 2, 3]]);
translate([0,0,3.0]) linear_extrude(0.3999999999999999) polygon(points=[[13.9, 37.2], [13.9, 36.0], [12.7, 36.0], [12.7, 37.2]],paths=[[0, 1, 2, 3]]);
translate([0,0,3.0]) linear_extrude(0.3999999999999999) polygon(points=[[42.0, 7.9], [43.2, 7.9], [43.2, 6.7], [42.0, 6.7]],paths=[[0, 1, 2, 3]]);
translate([0,0,3.0]) linear_extrude(0.3999999999999999) polygon(points=[[42.0, 36.0], [42.0, 37.2], [43.2, 37.2], [43.2, 36.0]],paths=[[0, 1, 2, 3]]);
translate([0,0,3.4]) linear_extrude(0.8000000000000003) polygon(points=[[0.535898, 41.4], [0.826587, 41.835046], [1.171573, 42.228427], [1.564954, 42.573413], [2.0, 42.864102], [2.469266, 43.095518], [2.964724, 43.263703], [3.477895, 43.365779], [4.0, 43.4], [59.4, 43.4], [59.922105, 43.365779], [60.435276, 43.263703], [60.930734, 43.095518], [61.4, 42.864102], [61.835046, 42.573413], [62.228427, 42.228427], [62.573413, 41.835046], [62.864102, 41.4], [63.095518, 40.930734], [63.263703, 40.435276], [63.365779, 39.922105], [63.4, 39.4], [63.4, 4.0], [63.365779, 3.477895], [63.263703, 2.964724], [63.095518, 2.469266], [62.864102, 2.0], [62.573413, 1.564954], [62.228427, 1.171573], [61.835046, 0.826587], [61.4, 0.535898], [60.930734, 0.304482], [60.435276, 0.136297], [59.922105, 0.034221], [59.4, 0.0], [4.0, 0.0], [3.477895, 0.034221], [2.964724, 0.136297], [2.469266, 0.304482], [2.0, 0.535898], [1.564954, 0.826587], [1.171573, 1.171573], [0.826587, 1.564954], [0.535898, 2.0], [0.304482, 2.469266], [0.136297, 2.964724], [0.034221, 3.477895], [0.0, 4.0], [0.0, 39.4], [0.034221, 39.922105], [0.136297, 40.435276], [0.304482, 40.930734], [59.891541, 2.843928], [59.5, 2.582309], [59.130315, 2.4], [59.4, 2.4], [59.608842, 2.413688], [59.81411, 2.454519], [60.012293, 2.521793], [60.2, 2.614359], [60.374018, 2.730635], [60.531371, 2.868629], [60.669365, 3.025982], [60.785641, 3.2], [60.878207, 3.387707], [60.945481, 3.58589], [60.986312, 3.791158], [61.0, 4.0], [61.0, 4.269685], [60.817691, 3.9], [60.556072, 3.508459], [60.245584, 3.154416], [59.5, 40.817691], [59.891541, 40.556072], [60.245584, 40.245584], [60.556072, 39.891541], [60.817691, 39.5], [61.0, 39.130315], [61.0, 39.4], [60.986312, 39.608842], [60.945481, 39.81411], [60.878207, 40.012293], [60.785641, 40.2], [60.669365, 40.374018], [60.531371, 40.531371], [60.374018, 40.669365], [60.2, 40.785641], [60.012293, 40.878207], [59.81411, 40.945481], [59.608842, 40.986312], [59.4, 41.0], [59.130315, 41.0], [9.025966, 36.32234], [8.817691, 35.9], [8.556072, 35.508459], [8.245584, 35.154416], [7.891541, 34.843928], [7.5, 34.582309], [7.07766, 34.374034], [6.631749, 34.222667], [6.169894, 34.130798], [5.7, 34.1], [5.230106, 34.130798], [4.768251, 34.222667], [4.32234, 34.374034], [3.9, 34.582309], [3.508459, 34.843928], [3.154416, 35.154416], [2.843928, 35.508459], [2.582309, 35.9], [2.4, 36.269685], [2.4, 7.130315], [2.582309, 7.5], [2.843928, 7.891541], [3.154416, 8.245584], [3.508459, 8.556072], [3.9, 8.817691], [4.32234, 9.025966], [4.768251, 9.177333], [5.230106, 9.269202], [5.7, 9.3], [6.169894, 9.269202], [6.631749, 9.177333], [7.07766, 9.025966], [7.5, 8.817691], [7.891541, 8.556072], [8.245584, 8.245584], [8.556072, 7.891541], [8.817691, 7.5], [9.025966, 7.07766], [9.177333, 6.631749], [9.269202, 6.169894], [9.3, 5.7], [9.269202, 5.230106], [9.177333, 4.768251], [9.025966, 4.32234], [8.817691, 3.9], [8.556072, 3.508459], [8.245584, 3.154416], [7.891541, 2.843928], [7.5, 2.582309], [7.130315, 2.4], [56.269685, 2.4], [55.9, 2.582309], [55.508459, 2.843928], [55.154416, 3.154416], [54.843928, 3.508459], [54.582309, 3.9], [54.374034, 4.32234], [54.222667, 4.768251], [54.130798, 5.230106], [54.1, 5.7], [54.130798, 6.169894], [54.222667, 6.631749], [54.374034, 7.07766], [54.582309, 7.5], [54.843928, 7.891541], [55.154416, 8.245584], [55.508459, 8.556072], [55.9, 8.817691], [56.32234, 9.025966], [56.768251, 9.177333], [57.230106, 9.269202], [57.7, 9.3], [58.169894, 9.269202], [58.631749, 9.177333], [59.07766, 9.025966], [59.5, 8.817691], [59.891541, 8.556072], [60.245584, 8.245584], [60.556072, 7.891541], [60.817691, 7.5], [61.0, 7.130315], [61.0, 36.269685], [60.817691, 35.9], [60.556072, 35.508459], [60.245584, 35.154416], [59.891541, 34.843928], [59.5, 34.582309], [59.07766, 34.374034], [58.631749, 34.222667], [58.169894, 34.130798], [57.7, 34.1], [57.230106, 34.130798], [56.768251, 34.222667], [56.32234, 34.374034], [55.9, 34.582309], [55.508459, 34.843928], [55.154416, 35.154416], [54.843928, 35.508459], [54.582309, 35.9], [54.374034, 36.32234], [54.222667, 36.768251], [54.130798, 37.230106], [54.1, 37.7], [54.130798, 38.169894], [54.222667, 38.631749], [54.374034, 39.07766], [54.582309, 39.5], [54.843928, 39.891541], [55.154416, 40.245584], [55.508459, 40.556072], [55.9, 40.817691], [56.269685, 41.0], [7.130315, 41.0], [7.5, 40.817691], [7.891541, 40.556072], [8.245584, 40.245584], [8.556072, 39.891541], [8.817691, 39.5], [9.025966, 39.07766], [9.177333, 38.631749], [9.269202, 38.169894], [9.3, 37.7], [9.269202, 37.230106], [9.177333, 36.768251], [2.4, 39.130315], [2.582309, 39.5], [2.843928, 39.891541], [3.154416, 40.245584], [3.508459, 40.556072], [3.9, 40.817691], [4.269685, 41.0], [4.0, 41.0], [3.791158, 40.986312], [3.58589, 40.945481], [3.387707, 40.878207], [3.2, 40.785641], [3.025982, 40.669365], [2.868629, 40.531371], [2.730635, 40.374018], [2.614359, 40.2], [2.521793, 40.012293], [2.454519, 39.81411], [2.413688, 39.608842], [2.4, 39.4], [3.508459, 2.843928], [3.154416, 3.154416], [2.843928, 3.508459], [2.582309, 3.9], [2.4, 4.269685], [2.4, 4.0], [2.413688, 3.791158], [2.454519, 3.58589], [2.521793, 3.387707], [2.614359, 3.2], [2.730635, 3.025982], [2.868629, 2.868629], [3.025982, 2.730635], [3.2, 2.614359], [3.387707, 2.521793], [3.58589, 2.454519], [3.791158, 2.413688], [4.0, 2.4], [4.269685, 2.4], [3.9, 2.582309]],paths=[[0, 1, 2, 3, 4, 5, 6, 7, 8, 9, 10, 11, 12, 13, 14, 15, 16, 17, 18, 19, 20, 21, 22, 23, 24, 25, 26, 27, 28, 29, 30, 31, 32, 33, 34, 35, 36, 37, 38, 39, 40, 41, 42, 43, 44, 45, 46, 47, 48, 49, 50, 51], [52, 53, 54, 55, 56, 57, 58, 59, 60, 61, 62, 63, 64, 65, 66, 67, 68, 69, 70, 71], [72, 73, 74, 75, 76, 77, 78, 79, 80, 81, 82, 83, 84, 85, 86, 87, 88, 89, 90, 91], [92, 93, 94, 95, 96, 97, 98, 99, 100, 101, 102, 103, 104, 105, 106, 107, 108, 109, 110, 111, 112, 113, 114, 115, 116, 117, 118, 119, 120, 121, 122, 123, 124, 125, 126, 127, 128, 129, 130, 131, 132, 133, 134, 135, 136, 137, 138, 139, 140, 141, 142, 143, 144, 145, 146, 147, 148, 149, 150, 151, 152, 153, 154, 155, 156, 157, 158, 159, 160, 161, 162, 163, 164, 165, 166, 167, 168, 169, 170, 171, 172, 173, 174, 175, 176, 177, 178, 179, 180, 181, 182, 183, 184, 185, 186, 187, 188, 189, 190, 191, 192, 193, 194, 195, 196, 197, 198, 199, 200, 201, 202, 203, 204, 205, 206, 207, 208, 209, 210, 211, 212, 213, 214, 215], [216, 217, 218, 219, 220, 221, 222, 223, 224, 225, 226, 227, 228, 229, 230, 231, 232, 233, 234, 235], [236, 237, 238, 239, 240, 241, 242, 243, 244, 245, 246, 247, 248, 249, 250, 251, 252, 253, 254, 255]]);
translate([0,0,3.4]) linear_extrude(0.8000000000000003) polygon(points=[[9.7, 12.5], [9.412842, 12.518821], [9.130598, 12.574963], [8.858096, 12.667465], [8.6, 12.794744], [8.360725, 12.954623], [8.144365, 13.144365], [7.954623, 13.360725], [7.794744, 13.6], [7.667465, 13.858096], [7.574963, 14.130598], [7.518821, 14.412842], [7.5, 14.7], [7.518821, 14.987158], [7.574963, 15.269402], [7.667465, 15.541904], [7.794744, 15.8], [7.954623, 16.039275], [8.144365, 16.255635], [8.360725, 16.445377], [8.6, 16.605256], [8.858096, 16.732535], [9.130598, 16.825037], [9.412842, 16.881179], [9.7, 16.9], [9.987158, 16.881179], [10.269402, 16.825037], [10.541904, 16.732535], [10.8, 16.605256], [11.039275, 16.445377], [11.255635, 16.255635], [11.445377, 16.039275], [11.605256, 15.8], [11.732535, 15.541904], [11.825037, 15.269402], [11.881179, 14.987158], [11.9, 14.7], [11.881179, 14.412842], [11.825037, 14.130598], [11.732535, 13.858096], [11.605256, 13.6], [11.445377, 13.360725], [11.255635, 13.144365], [11.039275, 12.954623], [10.8, 12.794744], [10.541904, 12.667465], [10.269402, 12.574963], [9.987158, 12.518821], [9.804421, 15.493156], [9.7, 15.5], [9.595579, 15.493156], [9.492945, 15.472741], [9.393853, 15.439104], [9.3, 15.39282], [9.212991, 15.334683], [9.134315, 15.265685], [9.065317, 15.187009], [9.00718, 15.1], [8.960896, 15.006147], [8.927259, 14.907055], [8.906844, 14.804421], [8.9, 14.7], [8.906844, 14.595579], [8.927259, 14.492945], [8.960896, 14.393853], [9.00718, 14.3], [9.065317, 14.212991], [9.134315, 14.134315], [9.212991, 14.065317], [9.3, 14.00718], [9.393853, 13.960896], [9.492945, 13.927259], [9.595579, 13.906844], [9.7, 13.9], [9.804421, 13.906844], [9.907055, 13.927259], [10.006147, 13.960896], [10.1, 14.00718], [10.187009, 14.065317], [10.265685, 14.134315], [10.334683, 14.212991], [10.39282, 14.3], [10.439104, 14.393853], [10.472741, 14.492945], [10.493156, 14.595579], [10.5, 14.7], [10.493156, 14.804421], [10.472741, 14.907055], [10.439104, 15.006147], [10.39282, 15.1], [10.334683, 15.187009], [10.265685, 15.265685], [10.187009, 15.334683], [10.1, 15.39282], [10.006147, 15.439104], [9.907055, 15.472741]],paths=[[0, 1, 2, 3, 4, 5, 6, 7, 8, 9, 10, 11, 12, 13, 14, 15, 16, 17, 18, 19, 20, 21, 22, 23, 24, 25, 26, 27, 28, 29, 30, 31, 32, 33, 34, 35, 36, 37, 38, 39, 40, 41, 42, 43, 44, 45, 46, 47], [48, 49, 50, 51, 52, 53, 54, 55, 56, 57, 58, 59, 60, 61, 62, 63, 64, 65, 66, 67, 68, 69, 70, 71, 72, 73, 74, 75, 76, 77, 78, 79, 80, 81, 82, 83, 84, 85, 86, 87, 88, 89, 90, 91, 92, 93, 94, 95]]);
translate([0,0,3.4]) linear_extrude(0.8000000000000003) polygon(points=[[10.269402, 27.074963], [9.987158, 27.018821], [9.7, 27.0], [9.412842, 27.018821], [9.130598, 27.074963], [8.858096, 27.167465], [8.6, 27.294744], [8.360725, 27.454623], [8.144365, 27.644365], [7.954623, 27.860725], [7.794744, 28.1], [7.667465, 28.358096], [7.574963, 28.630598], [7.518821, 28.912842], [7.5, 29.2], [7.518821, 29.487158], [7.574963, 29.769402], [7.667465, 30.041904], [7.794744, 30.3], [7.954623, 30.539275], [8.144365, 30.755635], [8.360725, 30.945377], [8.6, 31.105256], [8.858096, 31.232535], [9.130598, 31.325037], [9.412842, 31.381179], [9.7, 31.4], [9.987158, 31.381179], [10.269402, 31.325037], [10.541904, 31.232535], [10.8, 31.105256], [11.039275, 30.945377], [11.255635, 30.755635], [11.445377, 30.539275], [11.605256, 30.3], [11.732535, 30.041904], [11.825037, 29.769402], [11.881179, 29.487158], [11.9, 29.2], [11.881179, 28.912842], [11.825037, 28.630598], [11.732535, 28.358096], [11.605256, 28.1], [11.445377, 27.860725], [11.255635, 27.644365], [11.039275, 27.454623], [10.8, 27.294744], [10.541904, 27.167465], [10.006147, 29.939104], [9.907055, 29.972741], [9.804421, 29.993156], [9.7, 30.0], [9.595579, 29.993156], [9.492945, 29.972741], [9.393853, 29.939104], [9.3, 29.89282], [9.212991, 29.834683], [9.134315, 29.765685], [9.065317, 29.687009], [9.00718, 29.6], [8.960896, 29.506147], [8.927259, 29.407055], [8.906844, 29.304421], [8.9, 29.2], [8.906844, 29.095579], [8.927259, 28.992945], [8.960896, 28.893853], [9.00718, 28.8], [9.065317, 28.712991], [9.134315, 28.634315], [9.212991, 28.565317], [9.3, 28.50718], [9.393853, 28.460896], [9.492945, 28.427259], [9.595579, 28.406844], [9.7, 28.4], [9.804421, 28.406844], [9.907055, 28.427259], [10.006147, 28.460896], [10.1, 28.50718], [10.187009, 28.565317], [10.265685, 28.634315], [10.334683, 28.712991], [10.39282, 28.8], [10.439104, 28.893853], [10.472741, 28.992945], [10.493156, 29.095579], [10.5, 29.2], [10.493156, 29.304421], [10.472741, 29.407055], [10.439104, 29.506147], [10.39282, 29.6], [10.334683, 29.687009], [10.265685, 29.765685], [10.187009, 29.834683], [10.1, 29.89282]],paths=[[0, 1, 2, 3, 4, 5, 6, 7, 8, 9, 10, 11, 12, 13, 14, 15, 16, 17, 18, 19, 20, 21, 22, 23, 24, 25, 26, 27, 28, 29, 30, 31, 32, 33, 34, 35, 36, 37, 38, 39, 40, 41, 42, 43, 44, 45, 46, 47], [48, 49, 50, 51, 52, 53, 54, 55, 56, 57, 58, 59, 60, 61, 62, 63, 64, 65, 66, 67, 68, 69, 70, 71, 72, 73, 74, 75, 76, 77, 78, 79, 80, 81, 82, 83, 84, 85, 86, 87, 88, 89, 90, 91, 92, 93, 94, 95]]);
translate([0,0,3.4]) linear_extrude(0.8000000000000003) polygon(points=[[47.3, 12.794744], [47.041904, 12.667465], [46.769402, 12.574963], [46.487158, 12.518821], [46.2, 12.5], [45.912842, 12.518821], [45.630598, 12.574963], [45.358096, 12.667465], [45.1, 12.794744], [44.860725, 12.954623], [44.644365, 13.144365], [44.454623, 13.360725], [44.294744, 13.6], [44.167465, 13.858096], [44.074963, 14.130598], [44.018821, 14.412842], [44.0, 14.7], [44.018821, 14.987158], [44.074963, 15.269402], [44.167465, 15.541904], [44.294744, 15.8], [44.454623, 16.039275], [44.644365, 16.255635], [44.860725, 16.445377], [45.1, 16.605256], [45.358096, 16.732535], [45.630598, 16.825037], [45.912842, 16.881179], [46.2, 16.9], [46.487158, 16.881179], [46.769402, 16.825037], [47.041904, 16.732535], [47.3, 16.605256], [47.539275, 16.445377], [47.755635, 16.255635], [47.945377, 16.039275], [48.105256, 15.8], [48.232535, 15.541904], [48.325037, 15.269402], [48.381179, 14.987158], [48.4, 14.7], [48.381179, 14.412842], [48.325037, 14.130598], [48.232535, 13.858096], [48.105256, 13.6], [47.945377, 13.360725], [47.755635, 13.144365], [47.539275, 12.954623], [46.687009, 15.334683], [46.6, 15.39282], [46.506147, 15.439104], [46.407055, 15.472741], [46.304421, 15.493156], [46.2, 15.5], [46.095579, 15.493156], [45.992945, 15.472741], [45.893853, 15.439104], [45.8, 15.39282], [45.712991, 15.334683], [45.634315, 15.265685], [45.565317, 15.187009], [45.50718, 15.1], [45.460896, 15.006147], [45.427259, 14.907055], [45.406844, 14.804421], [45.4, 14.7], [45.406844, 14.595579], [45.427259, 14.492945], [45.460896, 14.393853], [45.50718, 14.3], [45.565317, 14.212991], [45.634315, 14.134315], [45.712991, 14.065317], [45.8, 14.00718], [45.893853, 13.960896], [45.992945, 13.927259], [46.095579, 13.906844], [46.2, 13.9], [46.304421, 13.906844], [46.407055, 13.927259], [46.506147, 13.960896], [46.6, 14.00718], [46.687009, 14.065317], [46.765685, 14.134315], [46.834683, 14.212991], [46.89282, 14.3], [46.939104, 14.393853], [46.972741, 14.492945], [46.993156, 14.595579], [47.0, 14.7], [46.993156, 14.804421], [46.972741, 14.907055], [46.939104, 15.006147], [46.89282, 15.1], [46.834683, 15.187009], [46.765685, 15.265685]],paths=[[0, 1, 2, 3, 4, 5, 6, 7, 8, 9, 10, 11, 12, 13, 14, 15, 16, 17, 18, 19, 20, 21, 22, 23, 24, 25, 26, 27, 28, 29, 30, 31, 32, 33, 34, 35, 36, 37, 38, 39, 40, 41, 42, 43, 44, 45, 46, 47], [48, 49, 50, 51, 52, 53, 54, 55, 56, 57, 58, 59, 60, 61, 62, 63, 64, 65, 66, 67, 68, 69, 70, 71, 72, 73, 74, 75, 76, 77, 78, 79, 80, 81, 82, 83, 84, 85, 86, 87, 88, 89, 90, 91, 92, 93, 94, 95]]);
translate([0,0,3.4]) linear_extrude(0.8000000000000003) polygon(points=[[47.755635, 27.644365], [47.539275, 27.454623], [47.3, 27.294744], [47.041904, 27.167465], [46.769402, 27.074963], [46.487158, 27.018821], [46.2, 27.0], [45.912842, 27.018821], [45.630598, 27.074963], [45.358096, 27.167465], [45.1, 27.294744], [44.860725, 27.454623], [44.644365, 27.644365], [44.454623, 27.860725], [44.294744, 28.1], [44.167465, 28.358096], [44.074963, 28.630598], [44.018821, 28.912842], [44.0, 29.2], [44.018821, 29.487158], [44.074963, 29.769402], [44.167465, 30.041904], [44.294744, 30.3], [44.454623, 30.539275], [44.644365, 30.755635], [44.860725, 30.945377], [45.1, 31.105256], [45.358096, 31.232535], [45.630598, 31.325037], [45.912842, 31.381179], [46.2, 31.4], [46.487158, 31.381179], [46.769402, 31.325037], [47.041904, 31.232535], [47.3, 31.105256], [47.539275, 30.945377], [47.755635, 30.755635], [47.945377, 30.539275], [48.105256, 30.3], [48.232535, 30.041904], [48.325037, 29.769402], [48.381179, 29.487158], [48.4, 29.2], [48.381179, 28.912842], [48.325037, 28.630598], [48.232535, 28.358096], [48.105256, 28.1], [47.945377, 27.860725], [46.834683, 29.687009], [46.765685, 29.765685], [46.687009, 29.834683], [46.6, 29.89282], [46.506147, 29.939104], [46.407055, 29.972741], [46.304421, 29.993156], [46.2, 30.0], [46.095579, 29.993156], [45.992945, 29.972741], [45.893853, 29.939104], [45.8, 29.89282], [45.712991, 29.834683], [45.634315, 29.765685], [45.565317, 29.687009], [45.50718, 29.6], [45.460896, 29.506147], [45.427259, 29.407055], [45.406844, 29.304421], [45.4, 29.2], [45.406844, 29.095579], [45.427259, 28.992945], [45.460896, 28.893853], [45.50718, 28.8], [45.565317, 28.712991], [45.634315, 28.634315], [45.712991, 28.565317], [45.8, 28.50718], [45.893853, 28.460896], [45.992945, 28.427259], [46.095579, 28.406844], [46.2, 28.4], [46.304421, 28.406844], [46.407055, 28.427259], [46.506147, 28.460896], [46.6, 28.50718], [46.687009, 28.565317], [46.765685, 28.634315], [46.834683, 28.712991], [46.89282, 28.8], [46.939104, 28.893853], [46.972741, 28.992945], [46.993156, 29.095579], [47.0, 29.2], [46.993156, 29.304421], [46.972741, 29.407055], [46.939104, 29.506147], [46.89282, 29.6]],paths=[[0, 1, 2, 3, 4, 5, 6, 7, 8, 9, 10, 11, 12, 13, 14, 15, 16, 17, 18, 19, 20, 21, 22, 23, 24, 25, 26, 27, 28, 29, 30, 31, 32, 33, 34, 35, 36, 37, 38, 39, 40, 41, 42, 43, 44, 45, 46, 47], [48, 49, 50, 51, 52, 53, 54, 55, 56, 57, 58, 59, 60, 61, 62, 63, 64, 65, 66, 67, 68, 69, 70, 71, 72, 73, 74, 75, 76, 77, 78, 79, 80, 81, 82, 83, 84, 85, 86, 87, 88, 89, 90, 91, 92, 93, 94, 95]]);
translate([0,0,3.4]) linear_extrude(0.8000000000000003) polygon(points=[[13.9, 6.7], [12.7, 6.7], [12.7, 7.9], [13.9, 7.9]],paths=[[0, 1, 2, 3]]);
translate([0,0,3.4]) linear_extrude(0.8000000000000003) polygon(points=[[13.9, 37.2], [13.9, 36.0], [12.7, 36.0], [12.7, 37.2]],paths=[[0, 1, 2, 3]]);
translate([0,0,3.4]) linear_extrude(0.8000000000000003) polygon(points=[[42.0, 7.9], [43.2, 7.9], [43.2, 6.7], [42.0, 6.7]],paths=[[0, 1, 2, 3]]);
translate([0,0,3.4]) linear_extrude(0.8000000000000003) polygon(points=[[42.0, 36.0], [42.0, 37.2], [43.2, 37.2], [43.2, 36.0]],paths=[[0, 1, 2, 3]]);
translate([0,0,4.2]) linear_extrude(1.7999999999999998) polygon(points=[[3.154416, 8.245584], [3.508459, 8.556072], [3.9, 8.817691], [4.32234, 9.025966], [4.768251, 9.177333], [5.230106, 9.269202], [5.7, 9.3], [6.169894, 9.269202], [6.631749, 9.177333], [7.07766, 9.025966], [7.5, 8.817691], [7.891541, 8.556072], [8.245584, 8.245584], [8.556072, 7.891541], [8.817691, 7.5], [9.025966, 7.07766], [9.177333, 6.631749], [9.269202, 6.169894], [9.3, 5.7], [9.269202, 5.230106], [9.177333, 4.768251], [9.025966, 4.32234], [8.817691, 3.9], [8.556072, 3.508459], [8.245584, 3.154416], [7.891541, 2.843928], [7.5, 2.582309], [7.130315, 2.4], [56.269685, 2.4], [55.9, 2.582309], [55.508459, 2.843928], [55.154416, 3.154416], [54.843928, 3.508459], [54.582309, 3.9], [54.374034, 4.32234], [54.222667, 4.768251], [54.130798, 5.230106], [54.1, 5.7], [54.130798, 6.169894], [54.222667, 6.631749], [54.374034, 7.07766], [54.582309, 7.5], [54.843928, 7.891541], [55.154416, 8.245584], [55.508459, 8.556072], [55.9, 8.817691], [56.32234, 9.025966], [56.768251, 9.177333], [57.230106, 9.269202], [57.7, 9.3], [58.169894, 9.269202], [58.631749, 9.177333], [59.07766, 9.025966], [59.5, 8.817691], [59.891541, 8.556072], [60.245584, 8.245584], [60.556072, 7.891541], [60.817691, 7.5], [61.0, 7.130315], [61.0, 36.269685], [60.817691, 35.9], [60.556072, 35.508459], [60.245584, 35.154416], [59.891541, 34.843928], [59.5, 34.582309], [59.07766, 34.374034], [58.631749, 34.222667], [58.169894, 34.130798], [57.7, 34.1], [57.230106, 34.130798], [56.768251, 34.222667], [56.32234, 34.374034], [55.9, 34.582309], [55.508459, 34.843928], [55.154416, 35.154416], [54.843928, 35.508459], [54.582309, 35.9], [54.374034, 36.32234], [54.222667, 36.768251], [54.130798, 37.230106], [54.1, 37.7], [54.130798, 38.169894], [54.222667, 38.631749], [54.374034, 39.07766], [54.582309, 39.5], [54.843928, 39.891541], [55.154416, 40.245584], [55.508459, 40.556072], [55.9, 40.817691], [56.269685, 41.0], [7.130315, 41.0], [7.5, 40.817691], [7.891541, 40.556072], [8.245584, 40.245584], [8.556072, 39.891541], [8.817691, 39.5], [9.025966, 39.07766], [9.177333, 38.631749], [9.269202, 38.169894], [9.3, 37.7], [9.269202, 37.230106], [9.177333, 36.768251], [9.025966, 36.32234], [8.817691, 35.9], [8.556072, 35.508459], [8.245584, 35.154416], [7.891541, 34.843928], [7.5, 34.582309], [7.07766, 34.374034], [6.631749, 34.222667], [6.169894, 34.130798], [5.7, 34.1], [5.230106, 34.130798], [4.768251, 34.222667], [4.32234, 34.374034], [3.9, 34.582309], [3.508459, 34.843928], [3.154416, 35.154416], [2.843928, 35.508459], [2.582309, 35.9], [2.4, 36.269685], [2.4, 29.7], [0.0, 29.7], [0.0, 39.4], [0.034221, 39.922105], [0.136297, 40.435276], [0.304482, 40.930734], [0.535898, 41.4], [0.826587, 41.835046], [1.171573, 42.228427], [1.564954, 42.573413], [2.0, 42.864102], [2.469266, 43.095518], [2.964724, 43.263703], [3.477895, 43.365779], [4.0, 43.4], [59.4, 43.4], [59.922105, 43.365779], [60.435276, 43.263703], [60.930734, 43.095518], [61.4, 42.864102], [61.835046, 42.573413], [62.228427, 42.228427], [62.573413, 41.835046], [62.864102, 41.4], [63.095518, 40.930734], [63.263703, 40.435276], [63.365779, 39.922105], [63.4, 39.4], [63.4, 4.0], [63.365779, 3.477895], [63.263703, 2.964724], [63.095518, 2.469266], [62.864102, 2.0], [62.573413, 1.564954], [62.228427, 1.171573], [61.835046, 0.826587], [61.4, 0.535898], [60.930734, 0.304482], [60.435276, 0.136297], [59.922105, 0.034221], [59.4, 0.0], [4.0, 0.0], [3.477895, 0.034221], [2.964724, 0.136297], [2.469266, 0.304482], [2.0, 0.535898], [1.564954, 0.826587], [1.171573, 1.171573], [0.826587, 1.564954], [0.535898, 2.0], [0.304482, 2.469266], [0.136297, 2.964724], [0.034221, 3.477895], [0.0, 4.0], [0.0, 13.7], [2.4, 13.7], [2.4, 7.130315], [2.582309, 7.5], [2.843928, 7.891541], [59.5, 2.582309], [59.130315, 2.4], [59.4, 2.4], [59.608842, 2.413688], [59.81411, 2.454519], [60.012293, 2.521793], [60.2, 2.614359], [60.374018, 2.730635], [60.531371, 2.868629], [60.669365, 3.025982], [60.785641, 3.2], [60.878207, 3.387707], [60.945481, 3.58589], [60.986312, 3.791158], [61.0, 4.0], [61.0, 4.269685], [60.817691, 3.9], [60.556072, 3.508459], [60.245584, 3.154416], [59.891541, 2.843928], [59.891541, 40.556072], [60.245584, 40.245584], [60.556072, 39.891541], [60.817691, 39.5], [61.0, 39.130315], [61.0, 39.4], [60.986312, 39.608842], [60.945481, 39.81411], [60.878207, 40.012293], [60.785641, 40.2], [60.669365, 40.374018], [60.531371, 40.531371], [60.374018, 40.669365], [60.2, 40.785641], [60.012293, 40.878207], [59.81411, 40.945481], [59.608842, 40.986312], [59.4, 41.0], [59.130315, 41.0], [59.5, 40.817691], [2.582309, 39.5], [2.843928, 39.891541], [3.154416, 40.245584], [3.508459, 40.556072], [3.9, 40.817691], [4.269685, 41.0], [4.0, 41.0], [3.791158, 40.986312], [3.58589, 40.945481], [3.387707, 40.878207], [3.2, 40.785641], [3.025982, 40.669365], [2.868629, 40.531371], [2.730635, 40.374018], [2.614359, 40.2], [2.521793, 40.012293], [2.454519, 39.81411], [2.413688, 39.608842], [2.4, 39.4], [2.4, 39.130315], [3.154416, 3.154416], [2.843928, 3.508459], [2.582309, 3.9], [2.4, 4.269685], [2.4, 4.0], [2.413688, 3.791158], [2.454519, 3.58589], [2.521793, 3.387707], [2.614359, 3.2], [2.730635, 3.025982], [2.868629, 2.868629], [3.025982, 2.730635], [3.2, 2.614359], [3.387707, 2.521793], [3.58589, 2.454519], [3.791158, 2.413688], [4.0, 2.4], [4.269685, 2.4], [3.9, 2.582309], [3.508459, 2.843928]],paths=[[0, 1, 2, 3, 4, 5, 6, 7, 8, 9, 10, 11, 12, 13, 14, 15, 16, 17, 18, 19, 20, 21, 22, 23, 24, 25, 26, 27, 28, 29, 30, 31, 32, 33, 34, 35, 36, 37, 38, 39, 40, 41, 42, 43, 44, 45, 46, 47, 48, 49, 50, 51, 52, 53, 54, 55, 56, 57, 58, 59, 60, 61, 62, 63, 64, 65, 66, 67, 68, 69, 70, 71, 72, 73, 74, 75, 76, 77, 78, 79, 80, 81, 82, 83, 84, 85, 86, 87, 88, 89, 90, 91, 92, 93, 94, 95, 96, 97, 98, 99, 100, 101, 102, 103, 104, 105, 106, 107, 108, 109, 110, 111, 112, 113, 114, 115, 116, 117, 118, 119, 120, 121, 122, 123, 124, 125, 126, 127, 128, 129, 130, 131, 132, 133, 134, 135, 136, 137, 138, 139, 140, 141, 142, 143, 144, 145, 146, 147, 148, 149, 150, 151, 152, 153, 154, 155, 156, 157, 158, 159, 160, 161, 162, 163, 164, 165, 166, 167, 168, 169, 170, 171, 172, 173, 174, 175, 176, 177, 178, 179], [180, 181, 182, 183, 184, 185, 186, 187, 188, 189, 190, 191, 192, 193, 194, 195, 196, 197, 198, 199], [200, 201, 202, 203, 204, 205, 206, 207, 208, 209, 210, 211, 212, 213, 214, 215, 216, 217, 218, 219], [220, 221, 222, 223, 224, 225, 226, 227, 228, 229, 230, 231, 232, 233, 234, 235, 236, 237, 238, 239], [240, 241, 242, 243, 244, 245, 246, 247, 248, 249, 250, 251, 252, 253, 254, 255, 256, 257, 258, 259]]);
translate([0,0,4.2]) linear_extrude(1.7999999999999998) polygon(points=[[9.7, 12.5], [9.412842, 12.518821], [9.130598, 12.574963], [8.858096, 12.667465], [8.6, 12.794744], [8.360725, 12.954623], [8.144365, 13.144365], [7.954623, 13.360725], [7.794744, 13.6], [7.667465, 13.858096], [7.574963, 14.130598], [7.518821, 14.412842], [7.5, 14.7], [7.518821, 14.987158], [7.574963, 15.269402], [7.667465, 15.541904], [7.794744, 15.8], [7.954623, 16.039275], [8.144365, 16.255635], [8.360725, 16.445377], [8.6, 16.605256], [8.858096, 16.732535], [9.130598, 16.825037], [9.412842, 16.881179], [9.7, 16.9], [9.987158, 16.881179], [10.269402, 16.825037], [10.541904, 16.732535], [10.8, 16.605256], [11.039275, 16.445377], [11.255635, 16.255635], [11.445377, 16.039275], [11.605256, 15.8], [11.732535, 15.541904], [11.825037, 15.269402], [11.881179, 14.987158], [11.9, 14.7], [11.881179, 14.412842], [11.825037, 14.130598], [11.732535, 13.858096], [11.605256, 13.6], [11.445377, 13.360725], [11.255635, 13.144365], [11.039275, 12.954623], [10.8, 12.794744], [10.541904, 12.667465], [10.269402, 12.574963], [9.987158, 12.518821], [9.804421, 15.493156], [9.7, 15.5], [9.595579, 15.493156], [9.492945, 15.472741], [9.393853, 15.439104], [9.3, 15.39282], [9.212991, 15.334683], [9.134315, 15.265685], [9.065317, 15.187009], [9.00718, 15.1], [8.960896, 15.006147], [8.927259, 14.907055], [8.906844, 14.804421], [8.9, 14.7], [8.906844, 14.595579], [8.927259, 14.492945], [8.960896, 14.393853], [9.00718, 14.3], [9.065317, 14.212991], [9.134315, 14.134315], [9.212991, 14.065317], [9.3, 14.00718], [9.393853, 13.960896], [9.492945, 13.927259], [9.595579, 13.906844], [9.7, 13.9], [9.804421, 13.906844], [9.907055, 13.927259], [10.006147, 13.960896], [10.1, 14.00718], [10.187009, 14.065317], [10.265685, 14.134315], [10.334683, 14.212991], [10.39282, 14.3], [10.439104, 14.393853], [10.472741, 14.492945], [10.493156, 14.595579], [10.5, 14.7], [10.493156, 14.804421], [10.472741, 14.907055], [10.439104, 15.006147], [10.39282, 15.1], [10.334683, 15.187009], [10.265685, 15.265685], [10.187009, 15.334683], [10.1, 15.39282], [10.006147, 15.439104], [9.907055, 15.472741]],paths=[[0, 1, 2, 3, 4, 5, 6, 7, 8, 9, 10, 11, 12, 13, 14, 15, 16, 17, 18, 19, 20, 21, 22, 23, 24, 25, 26, 27, 28, 29, 30, 31, 32, 33, 34, 35, 36, 37, 38, 39, 40, 41, 42, 43, 44, 45, 46, 47], [48, 49, 50, 51, 52, 53, 54, 55, 56, 57, 58, 59, 60, 61, 62, 63, 64, 65, 66, 67, 68, 69, 70, 71, 72, 73, 74, 75, 76, 77, 78, 79, 80, 81, 82, 83, 84, 85, 86, 87, 88, 89, 90, 91, 92, 93, 94, 95]]);
translate([0,0,4.2]) linear_extrude(1.7999999999999998) polygon(points=[[10.269402, 27.074963], [9.987158, 27.018821], [9.7, 27.0], [9.412842, 27.018821], [9.130598, 27.074963], [8.858096, 27.167465], [8.6, 27.294744], [8.360725, 27.454623], [8.144365, 27.644365], [7.954623, 27.860725], [7.794744, 28.1], [7.667465, 28.358096], [7.574963, 28.630598], [7.518821, 28.912842], [7.5, 29.2], [7.518821, 29.487158], [7.574963, 29.769402], [7.667465, 30.041904], [7.794744, 30.3], [7.954623, 30.539275], [8.144365, 30.755635], [8.360725, 30.945377], [8.6, 31.105256], [8.858096, 31.232535], [9.130598, 31.325037], [9.412842, 31.381179], [9.7, 31.4], [9.987158, 31.381179], [10.269402, 31.325037], [10.541904, 31.232535], [10.8, 31.105256], [11.039275, 30.945377], [11.255635, 30.755635], [11.445377, 30.539275], [11.605256, 30.3], [11.732535, 30.041904], [11.825037, 29.769402], [11.881179, 29.487158], [11.9, 29.2], [11.881179, 28.912842], [11.825037, 28.630598], [11.732535, 28.358096], [11.605256, 28.1], [11.445377, 27.860725], [11.255635, 27.644365], [11.039275, 27.454623], [10.8, 27.294744], [10.541904, 27.167465], [10.006147, 29.939104], [9.907055, 29.972741], [9.804421, 29.993156], [9.7, 30.0], [9.595579, 29.993156], [9.492945, 29.972741], [9.393853, 29.939104], [9.3, 29.89282], [9.212991, 29.834683], [9.134315, 29.765685], [9.065317, 29.687009], [9.00718, 29.6], [8.960896, 29.506147], [8.927259, 29.407055], [8.906844, 29.304421], [8.9, 29.2], [8.906844, 29.095579], [8.927259, 28.992945], [8.960896, 28.893853], [9.00718, 28.8], [9.065317, 28.712991], [9.134315, 28.634315], [9.212991, 28.565317], [9.3, 28.50718], [9.393853, 28.460896], [9.492945, 28.427259], [9.595579, 28.406844], [9.7, 28.4], [9.804421, 28.406844], [9.907055, 28.427259], [10.006147, 28.460896], [10.1, 28.50718], [10.187009, 28.565317], [10.265685, 28.634315], [10.334683, 28.712991], [10.39282, 28.8], [10.439104, 28.893853], [10.472741, 28.992945], [10.493156, 29.095579], [10.5, 29.2], [10.493156, 29.304421], [10.472741, 29.407055], [10.439104, 29.506147], [10.39282, 29.6], [10.334683, 29.687009], [10.265685, 29.765685], [10.187009, 29.834683], [10.1, 29.89282]],paths=[[0, 1, 2, 3, 4, 5, 6, 7, 8, 9, 10, 11, 12, 13, 14, 15, 16, 17, 18, 19, 20, 21, 22, 23, 24, 25, 26, 27, 28, 29, 30, 31, 32, 33, 34, 35, 36, 37, 38, 39, 40, 41, 42, 43, 44, 45, 46, 47], [48, 49, 50, 51, 52, 53, 54, 55, 56, 57, 58, 59, 60, 61, 62, 63, 64, 65, 66, 67, 68, 69, 70, 71, 72, 73, 74, 75, 76, 77, 78, 79, 80, 81, 82, 83, 84, 85, 86, 87, 88, 89, 90, 91, 92, 93, 94, 95]]);
translate([0,0,4.2]) linear_extrude(1.7999999999999998) polygon(points=[[47.3, 12.794744], [47.041904, 12.667465], [46.769402, 12.574963], [46.487158, 12.518821], [46.2, 12.5], [45.912842, 12.518821], [45.630598, 12.574963], [45.358096, 12.667465], [45.1, 12.794744], [44.860725, 12.954623], [44.644365, 13.144365], [44.454623, 13.360725], [44.294744, 13.6], [44.167465, 13.858096], [44.074963, 14.130598], [44.018821, 14.412842], [44.0, 14.7], [44.018821, 14.987158], [44.074963, 15.269402], [44.167465, 15.541904], [44.294744, 15.8], [44.454623, 16.039275], [44.644365, 16.255635], [44.860725, 16.445377], [45.1, 16.605256], [45.358096, 16.732535], [45.630598, 16.825037], [45.912842, 16.881179], [46.2, 16.9], [46.487158, 16.881179], [46.769402, 16.825037], [47.041904, 16.732535], [47.3, 16.605256], [47.539275, 16.445377], [47.755635, 16.255635], [47.945377, 16.039275], [48.105256, 15.8], [48.232535, 15.541904], [48.325037, 15.269402], [48.381179, 14.987158], [48.4, 14.7], [48.381179, 14.412842], [48.325037, 14.130598], [48.232535, 13.858096], [48.105256, 13.6], [47.945377, 13.360725], [47.755635, 13.144365], [47.539275, 12.954623], [46.687009, 15.334683], [46.6, 15.39282], [46.506147, 15.439104], [46.407055, 15.472741], [46.304421, 15.493156], [46.2, 15.5], [46.095579, 15.493156], [45.992945, 15.472741], [45.893853, 15.439104], [45.8, 15.39282], [45.712991, 15.334683], [45.634315, 15.265685], [45.565317, 15.187009], [45.50718, 15.1], [45.460896, 15.006147], [45.427259, 14.907055], [45.406844, 14.804421], [45.4, 14.7], [45.406844, 14.595579], [45.427259, 14.492945], [45.460896, 14.393853], [45.50718, 14.3], [45.565317, 14.212991], [45.634315, 14.134315], [45.712991, 14.065317], [45.8, 14.00718], [45.893853, 13.960896], [45.992945, 13.927259], [46.095579, 13.906844], [46.2, 13.9], [46.304421, 13.906844], [46.407055, 13.927259], [46.506147, 13.960896], [46.6, 14.00718], [46.687009, 14.065317], [46.765685, 14.134315], [46.834683, 14.212991], [46.89282, 14.3], [46.939104, 14.393853], [46.972741, 14.492945], [46.993156, 14.595579], [47.0, 14.7], [46.993156, 14.804421], [46.972741, 14.907055], [46.939104, 15.006147], [46.89282, 15.1], [46.834683, 15.187009], [46.765685, 15.265685]],paths=[[0, 1, 2, 3, 4, 5, 6, 7, 8, 9, 10, 11, 12, 13, 14, 15, 16, 17, 18, 19, 20, 21, 22, 23, 24, 25, 26, 27, 28, 29, 30, 31, 32, 33, 34, 35, 36, 37, 38, 39, 40, 41, 42, 43, 44, 45, 46, 47], [48, 49, 50, 51, 52, 53, 54, 55, 56, 57, 58, 59, 60, 61, 62, 63, 64, 65, 66, 67, 68, 69, 70, 71, 72, 73, 74, 75, 76, 77, 78, 79, 80, 81, 82, 83, 84, 85, 86, 87, 88, 89, 90, 91, 92, 93, 94, 95]]);
translate([0,0,4.2]) linear_extrude(1.7999999999999998) polygon(points=[[47.755635, 27.644365], [47.539275, 27.454623], [47.3, 27.294744], [47.041904, 27.167465], [46.769402, 27.074963], [46.487158, 27.018821], [46.2, 27.0], [45.912842, 27.018821], [45.630598, 27.074963], [45.358096, 27.167465], [45.1, 27.294744], [44.860725, 27.454623], [44.644365, 27.644365], [44.454623, 27.860725], [44.294744, 28.1], [44.167465, 28.358096], [44.074963, 28.630598], [44.018821, 28.912842], [44.0, 29.2], [44.018821, 29.487158], [44.074963, 29.769402], [44.167465, 30.041904], [44.294744, 30.3], [44.454623, 30.539275], [44.644365, 30.755635], [44.860725, 30.945377], [45.1, 31.105256], [45.358096, 31.232535], [45.630598, 31.325037], [45.912842, 31.381179], [46.2, 31.4], [46.487158, 31.381179], [46.769402, 31.325037], [47.041904, 31.232535], [47.3, 31.105256], [47.539275, 30.945377], [47.755635, 30.755635], [47.945377, 30.539275], [48.105256, 30.3], [48.232535, 30.041904], [48.325037, 29.769402], [48.381179, 29.487158], [48.4, 29.2], [48.381179, 28.912842], [48.325037, 28.630598], [48.232535, 28.358096], [48.105256, 28.1], [47.945377, 27.860725], [46.834683, 29.687009], [46.765685, 29.765685], [46.687009, 29.834683], [46.6, 29.89282], [46.506147, 29.939104], [46.407055, 29.972741], [46.304421, 29.993156], [46.2, 30.0], [46.095579, 29.993156], [45.992945, 29.972741], [45.893853, 29.939104], [45.8, 29.89282], [45.712991, 29.834683], [45.634315, 29.765685], [45.565317, 29.687009], [45.50718, 29.6], [45.460896, 29.506147], [45.427259, 29.407055], [45.406844, 29.304421], [45.4, 29.2], [45.406844, 29.095579], [45.427259, 28.992945], [45.460896, 28.893853], [45.50718, 28.8], [45.565317, 28.712991], [45.634315, 28.634315], [45.712991, 28.565317], [45.8, 28.50718], [45.893853, 28.460896], [45.992945, 28.427259], [46.095579, 28.406844], [46.2, 28.4], [46.304421, 28.406844], [46.407055, 28.427259], [46.506147, 28.460896], [46.6, 28.50718], [46.687009, 28.565317], [46.765685, 28.634315], [46.834683, 28.712991], [46.89282, 28.8], [46.939104, 28.893853], [46.972741, 28.992945], [46.993156, 29.095579], [47.0, 29.2], [46.993156, 29.304421], [46.972741, 29.407055], [46.939104, 29.506147], [46.89282, 29.6]],paths=[[0, 1, 2, 3, 4, 5, 6, 7, 8, 9, 10, 11, 12, 13, 14, 15, 16, 17, 18, 19, 20, 21, 22, 23, 24, 25, 26, 27, 28, 29, 30, 31, 32, 33, 34, 35, 36, 37, 38, 39, 40, 41, 42, 43, 44, 45, 46, 47], [48, 49, 50, 51, 52, 53, 54, 55, 56, 57, 58, 59, 60, 61, 62, 63, 64, 65, 66, 67, 68, 69, 70, 71, 72, 73, 74, 75, 76, 77, 78, 79, 80, 81, 82, 83, 84, 85, 86, 87, 88, 89, 90, 91, 92, 93, 94, 95]]);
translate([0,0,4.2]) linear_extrude(1.7999999999999998) polygon(points=[[13.9, 6.7], [12.7, 6.7], [12.7, 7.9], [13.9, 7.9]],paths=[[0, 1, 2, 3]]);
translate([0,0,4.2]) linear_extrude(1.7999999999999998) polygon(points=[[13.9, 37.2], [13.9, 36.0], [12.7, 36.0], [12.7, 37.2]],paths=[[0, 1, 2, 3]]);
translate([0,0,4.2]) linear_extrude(1.7999999999999998) polygon(points=[[42.0, 7.9], [43.2, 7.9], [43.2, 6.7], [42.0, 6.7]],paths=[[0, 1, 2, 3]]);
translate([0,0,4.2]) linear_extrude(1.7999999999999998) polygon(points=[[42.0, 36.0], [42.0, 37.2], [43.2, 37.2], [43.2, 36.0]],paths=[[0, 1, 2, 3]]);
translate([0,0,6.0]) linear_extrude(1.5999999999999996) polygon(points=[[2.4, 13.7], [2.4, 7.130315], [2.582309, 7.5], [2.843928, 7.891541], [3.154416, 8.245584], [3.508459, 8.556072], [3.9, 8.817691], [4.32234, 9.025966], [4.768251, 9.177333], [5.230106, 9.269202], [5.7, 9.3], [6.169894, 9.269202], [6.631749, 9.177333], [7.07766, 9.025966], [7.5, 8.817691], [7.891541, 8.556072], [8.245584, 8.245584], [8.556072, 7.891541], [8.817691, 7.5], [9.025966, 7.07766], [9.177333, 6.631749], [9.269202, 6.169894], [9.3, 5.7], [9.269202, 5.230106], [9.177333, 4.768251], [9.025966, 4.32234], [8.817691, 3.9], [8.556072, 3.508459], [8.245584, 3.154416], [7.891541, 2.843928], [7.5, 2.582309], [7.130315, 2.4], [56.269685, 2.4], [55.9, 2.582309], [55.508459, 2.843928], [55.154416, 3.154416], [54.843928, 3.508459], [54.582309, 3.9], [54.374034, 4.32234], [54.222667, 4.768251], [54.130798, 5.230106], [54.1, 5.7], [54.130798, 6.169894], [54.222667, 6.631749], [54.374034, 7.07766], [54.582309, 7.5], [54.843928, 7.891541], [55.154416, 8.245584], [55.508459, 8.556072], [55.9, 8.817691], [56.32234, 9.025966], [56.768251, 9.177333], [57.230106, 9.269202], [57.7, 9.3], [58.169894, 9.269202], [58.631749, 9.177333], [59.07766, 9.025966], [59.5, 8.817691], [59.891541, 8.556072], [60.245584, 8.245584], [60.556072, 7.891541], [60.817691, 7.5], [61.0, 7.130315], [61.0, 36.269685], [60.817691, 35.9], [60.556072, 35.508459], [60.245584, 35.154416], [59.891541, 34.843928], [59.5, 34.582309], [59.07766, 34.374034], [58.631749, 34.222667], [58.169894, 34.130798], [57.7, 34.1], [57.230106, 34.130798], [56.768251, 34.222667], [56.32234, 34.374034], [55.9, 34.582309], [55.508459, 34.843928], [55.154416, 35.154416], [54.843928, 35.508459], [54.582309, 35.9], [54.374034, 36.32234], [54.222667, 36.768251], [54.130798, 37.230106], [54.1, 37.7], [54.130798, 38.169894], [54.222667, 38.631749], [54.374034, 39.07766], [54.582309, 39.5], [54.843928, 39.891541], [55.154416, 40.245584], [55.508459, 40.556072], [55.9, 40.817691], [56.269685, 41.0], [7.130315, 41.0], [7.5, 40.817691], [7.891541, 40.556072], [8.245584, 40.245584], [8.556072, 39.891541], [8.817691, 39.5], [9.025966, 39.07766], [9.177333, 38.631749], [9.269202, 38.169894], [9.3, 37.7], [9.269202, 37.230106], [9.177333, 36.768251], [9.025966, 36.32234], [8.817691, 35.9], [8.556072, 35.508459], [8.245584, 35.154416], [7.891541, 34.843928], [7.5, 34.582309], [7.07766, 34.374034], [6.631749, 34.222667], [6.169894, 34.130798], [5.7, 34.1], [5.230106, 34.130798], [4.768251, 34.222667], [4.32234, 34.374034], [3.9, 34.582309], [3.508459, 34.843928], [3.154416, 35.154416], [2.843928, 35.508459], [2.582309, 35.9], [2.4, 36.269685], [2.4, 29.7], [0.0, 29.7], [0.0, 39.4], [0.034221, 39.922105], [0.136297, 40.435276], [0.304482, 40.930734], [0.535898, 41.4], [0.826587, 41.835046], [1.171573, 42.228427], [1.564954, 42.573413], [2.0, 42.864102], [2.469266, 43.095518], [2.964724, 43.263703], [3.477895, 43.365779], [4.0, 43.4], [59.4, 43.4], [59.922105, 43.365779], [60.435276, 43.263703], [60.930734, 43.095518], [61.4, 42.864102], [61.835046, 42.573413], [62.228427, 42.228427], [62.573413, 41.835046], [62.864102, 41.4], [63.095518, 40.930734], [63.263703, 40.435276], [63.365779, 39.922105], [63.4, 39.4], [63.4, 4.0], [63.365779, 3.477895], [63.263703, 2.964724], [63.095518, 2.469266], [62.864102, 2.0], [62.573413, 1.564954], [62.228427, 1.171573], [61.835046, 0.826587], [61.4, 0.535898], [60.930734, 0.304482], [60.435276, 0.136297], [59.922105, 0.034221], [59.4, 0.0], [4.0, 0.0], [3.477895, 0.034221], [2.964724, 0.136297], [2.469266, 0.304482], [2.0, 0.535898], [1.564954, 0.826587], [1.171573, 1.171573], [0.826587, 1.564954], [0.535898, 2.0], [0.304482, 2.469266], [0.136297, 2.964724], [0.034221, 3.477895], [0.0, 4.0], [0.0, 13.7], [60.817691, 3.9], [60.556072, 3.508459], [60.245584, 3.154416], [59.891541, 2.843928], [59.5, 2.582309], [59.130315, 2.4], [59.4, 2.4], [59.608842, 2.413688], [59.81411, 2.454519], [60.012293, 2.521793], [60.2, 2.614359], [60.374018, 2.730635], [60.531371, 2.868629], [60.669365, 3.025982], [60.785641, 3.2], [60.878207, 3.387707], [60.945481, 3.58589], [60.986312, 3.791158], [61.0, 4.0], [61.0, 4.269685], [59.608842, 40.986312], [59.4, 41.0], [59.130315, 41.0], [59.5, 40.817691], [59.891541, 40.556072], [60.245584, 40.245584], [60.556072, 39.891541], [60.817691, 39.5], [61.0, 39.130315], [61.0, 39.4], [60.986312, 39.608842], [60.945481, 39.81411], [60.878207, 40.012293], [60.785641, 40.2], [60.669365, 40.374018], [60.531371, 40.531371], [60.374018, 40.669365], [60.2, 40.785641], [60.012293, 40.878207], [59.81411, 40.945481], [2.454519, 39.81411], [2.413688, 39.608842], [2.4, 39.4], [2.4, 39.130315], [2.582309, 39.5], [2.843928, 39.891541], [3.154416, 40.245584], [3.508459, 40.556072], [3.9, 40.817691], [4.269685, 41.0], [4.0, 41.0], [3.791158, 40.986312], [3.58589, 40.945481], [3.387707, 40.878207], [3.2, 40.785641], [3.025982, 40.669365], [2.868629, 40.531371], [2.730635, 40.374018], [2.614359, 40.2], [2.521793, 40.012293], [4.0, 2.4], [4.269685, 2.4], [3.9, 2.582309], [3.508459, 2.843928], [3.154416, 3.154416], [2.843928, 3.508459], [2.582309, 3.9], [2.4, 4.269685], [2.4, 4.0], [2.413688, 3.791158], [2.454519, 3.58589], [2.521793, 3.387707], [2.614359, 3.2], [2.730635, 3.025982], [2.868629, 2.868629], [3.025982, 2.730635], [3.2, 2.614359], [3.387707, 2.521793], [3.58589, 2.454519], [3.791158, 2.413688]],paths=[[0, 1, 2, 3, 4, 5, 6, 7, 8, 9, 10, 11, 12, 13, 14, 15, 16, 17, 18, 19, 20, 21, 22, 23, 24, 25, 26, 27, 28, 29, 30, 31, 32, 33, 34, 35, 36, 37, 38, 39, 40, 41, 42, 43, 44, 45, 46, 47, 48, 49, 50, 51, 52, 53, 54, 55, 56, 57, 58, 59, 60, 61, 62, 63, 64, 65, 66, 67, 68, 69, 70, 71, 72, 73, 74, 75, 76, 77, 78, 79, 80, 81, 82, 83, 84, 85, 86, 87, 88, 89, 90, 91, 92, 93, 94, 95, 96, 97, 98, 99, 100, 101, 102, 103, 104, 105, 106, 107, 108, 109, 110, 111, 112, 113, 114, 115, 116, 117, 118, 119, 120, 121, 122, 123, 124, 125, 126, 127, 128, 129, 130, 131, 132, 133, 134, 135, 136, 137, 138, 139, 140, 141, 142, 143, 144, 145, 146, 147, 148, 149, 150, 151, 152, 153, 154, 155, 156, 157, 158, 159, 160, 161, 162, 163, 164, 165, 166, 167, 168, 169, 170, 171, 172, 173, 174, 175, 176, 177, 178, 179], [180, 181, 182, 183, 184, 185, 186, 187, 188, 189, 190, 191, 192, 193, 194, 195, 196, 197, 198, 199], [200, 201, 202, 203, 204, 205, 206, 207, 208, 209, 210, 211, 212, 213, 214, 215, 216, 217, 218, 219], [220, 221, 222, 223, 224, 225, 226, 227, 228, 229, 230, 231, 232, 233, 234, 235, 236, 237, 238, 239], [240, 241, 242, 243, 244, 245, 246, 247, 248, 249, 250, 251, 252, 253, 254, 255, 256, 257, 258, 259]]);
translate([0,0,6.0]) linear_extrude(1.5999999999999996) polygon(points=[[10.8, 12.794744], [10.541904, 12.667465], [10.269402, 12.574963], [9.987158, 12.518821], [9.7, 12.5], [9.412842, 12.518821], [9.130598, 12.574963], [8.858096, 12.667465], [8.6, 12.794744], [8.360725, 12.954623], [8.144365, 13.144365], [7.954623, 13.360725], [7.794744, 13.6], [7.667465, 13.858096], [7.574963, 14.130598], [7.518821, 14.412842], [7.5, 14.7], [7.518821, 14.987158], [7.574963, 15.269402], [7.667465, 15.541904], [7.794744, 15.8], [7.954623, 16.039275], [8.144365, 16.255635], [8.360725, 16.445377], [8.6, 16.605256], [8.858096, 16.732535], [9.130598, 16.825037], [9.412842, 16.881179], [9.7, 16.9], [9.987158, 16.881179], [10.269402, 16.825037], [10.541904, 16.732535], [10.8, 16.605256], [11.039275, 16.445377], [11.255635, 16.255635], [11.445377, 16.039275], [11.605256, 15.8], [11.732535, 15.541904], [11.825037, 15.269402], [11.881179, 14.987158], [11.9, 14.7], [11.881179, 14.412842], [11.825037, 14.130598], [11.732535, 13.858096], [11.605256, 13.6], [11.445377, 13.360725], [11.255635, 13.144365], [11.039275, 12.954623], [10.187009, 15.334683], [10.1, 15.39282], [10.006147, 15.439104], [9.907055, 15.472741], [9.804421, 15.493156], [9.7, 15.5], [9.595579, 15.493156], [9.492945, 15.472741], [9.393853, 15.439104], [9.3, 15.39282], [9.212991, 15.334683], [9.134315, 15.265685], [9.065317, 15.187009], [9.00718, 15.1], [8.960896, 15.006147], [8.927259, 14.907055], [8.906844, 14.804421], [8.9, 14.7], [8.906844, 14.595579], [8.927259, 14.492945], [8.960896, 14.393853], [9.00718, 14.3], [9.065317, 14.212991], [9.134315, 14.134315], [9.212991, 14.065317], [9.3, 14.00718], [9.393853, 13.960896], [9.492945, 13.927259], [9.595579, 13.906844], [9.7, 13.9], [9.804421, 13.906844], [9.907055, 13.927259], [10.006147, 13.960896], [10.1, 14.00718], [10.187009, 14.065317], [10.265685, 14.134315], [10.334683, 14.212991], [10.39282, 14.3], [10.439104, 14.393853], [10.472741, 14.492945], [10.493156, 14.595579], [10.5, 14.7], [10.493156, 14.804421], [10.472741, 14.907055], [10.439104, 15.006147], [10.39282, 15.1], [10.334683, 15.187009], [10.265685, 15.265685]],paths=[[0, 1, 2, 3, 4, 5, 6, 7, 8, 9, 10, 11, 12, 13, 14, 15, 16, 17, 18, 19, 20, 21, 22, 23, 24, 25, 26, 27, 28, 29, 30, 31, 32, 33, 34, 35, 36, 37, 38, 39, 40, 41, 42, 43, 44, 45, 46, 47], [48, 49, 50, 51, 52, 53, 54, 55, 56, 57, 58, 59, 60, 61, 62, 63, 64, 65, 66, 67, 68, 69, 70, 71, 72, 73, 74, 75, 76, 77, 78, 79, 80, 81, 82, 83, 84, 85, 86, 87, 88, 89, 90, 91, 92, 93, 94, 95]]);
translate([0,0,6.0]) linear_extrude(1.5999999999999996) polygon(points=[[11.255635, 27.644365], [11.039275, 27.454623], [10.8, 27.294744], [10.541904, 27.167465], [10.269402, 27.074963], [9.987158, 27.018821], [9.7, 27.0], [9.412842, 27.018821], [9.130598, 27.074963], [8.858096, 27.167465], [8.6, 27.294744], [8.360725, 27.454623], [8.144365, 27.644365], [7.954623, 27.860725], [7.794744, 28.1], [7.667465, 28.358096], [7.574963, 28.630598], [7.518821, 28.912842], [7.5, 29.2], [7.518821, 29.487158], [7.574963, 29.769402], [7.667465, 30.041904], [7.794744, 30.3], [7.954623, 30.539275], [8.144365, 30.755635], [8.360725, 30.945377], [8.6, 31.105256], [8.858096, 31.232535], [9.130598, 31.325037], [9.412842, 31.381179], [9.7, 31.4], [9.987158, 31.381179], [10.269402, 31.325037], [10.541904, 31.232535], [10.8, 31.105256], [11.039275, 30.945377], [11.255635, 30.755635], [11.445377, 30.539275], [11.605256, 30.3], [11.732535, 30.041904], [11.825037, 29.769402], [11.881179, 29.487158], [11.9, 29.2], [11.881179, 28.912842], [11.825037, 28.630598], [11.732535, 28.358096], [11.605256, 28.1], [11.445377, 27.860725], [10.334683, 29.687009], [10.265685, 29.765685], [10.187009, 29.834683], [10.1, 29.89282], [10.006147, 29.939104], [9.907055, 29.972741], [9.804421, 29.993156], [9.7, 30.0], [9.595579, 29.993156], [9.492945, 29.972741], [9.393853, 29.939104], [9.3, 29.89282], [9.212991, 29.834683], [9.134315, 29.765685], [9.065317, 29.687009], [9.00718, 29.6], [8.960896, 29.506147], [8.927259, 29.407055], [8.906844, 29.304421], [8.9, 29.2], [8.906844, 29.095579], [8.927259, 28.992945], [8.960896, 28.893853], [9.00718, 28.8], [9.065317, 28.712991], [9.134315, 28.634315], [9.212991, 28.565317], [9.3, 28.50718], [9.393853, 28.460896], [9.492945, 28.427259], [9.595579, 28.406844], [9.7, 28.4], [9.804421, 28.406844], [9.907055, 28.427259], [10.006147, 28.460896], [10.1, 28.50718], [10.187009, 28.565317], [10.265685, 28.634315], [10.334683, 28.712991], [10.39282, 28.8], [10.439104, 28.893853], [10.472741, 28.992945], [10.493156, 29.095579], [10.5, 29.2], [10.493156, 29.304421], [10.472741, 29.407055], [10.439104, 29.506147], [10.39282, 29.6]],paths=[[0, 1, 2, 3, 4, 5, 6, 7, 8, 9, 10, 11, 12, 13, 14, 15, 16, 17, 18, 19, 20, 21, 22, 23, 24, 25, 26, 27, 28, 29, 30, 31, 32, 33, 34, 35, 36, 37, 38, 39, 40, 41, 42, 43, 44, 45, 46, 47], [48, 49, 50, 51, 52, 53, 54, 55, 56, 57, 58, 59, 60, 61, 62, 63, 64, 65, 66, 67, 68, 69, 70, 71, 72, 73, 74, 75, 76, 77, 78, 79, 80, 81, 82, 83, 84, 85, 86, 87, 88, 89, 90, 91, 92, 93, 94, 95]]);
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
