habakan/jitsu-in-pico/hardware/kicad/pico2h-carrier/pico2h_carrier.kicad_sch

## KiCad design hardware/kicad/pico2h-carrier/pico2h_carrier.kicad_sch (2026-10-10)

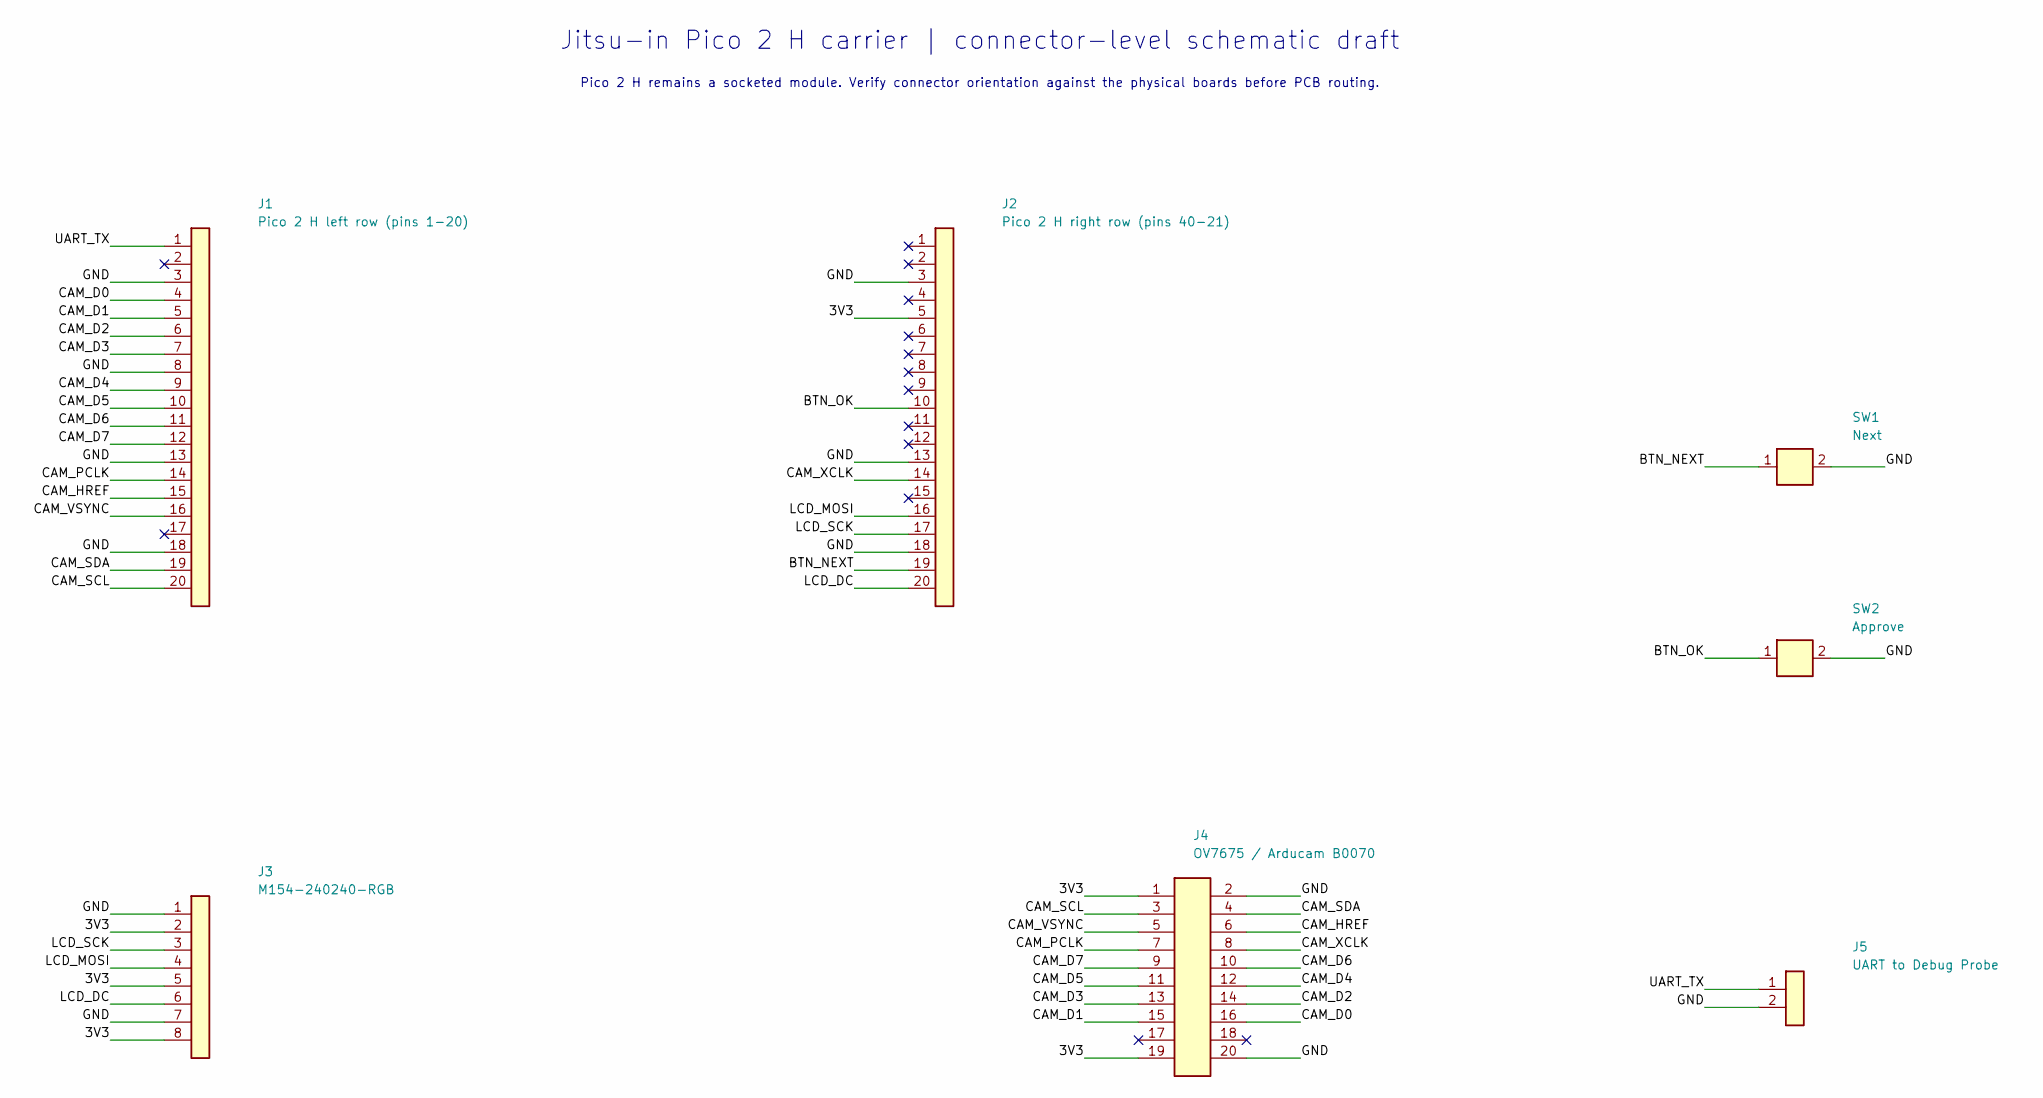
[picture p9: schematic pico2h_carrier.kicad_sch]

Parts:
J1: Pico 2 H left row (pins 1-20); PinSocket_1x20_P2.54mm_Vertical
J2: Pico 2 H right row (pins 40-21); PinSocket_1x20_P2.54mm_Vertical
J3: M154-240240-RGB; PinSocket_1x08_P2.54mm_Vertical
J4: OV7675 / Arducam B0070; PinSocket_2x10_P2.54mm_Vertical
J5: UART to Debug Probe; PinSocket_1x02_P2.54mm_Vertical
SW1: Next; SW_PUSH_6mm
SW2: Approve; SW_PUSH_6mm

Connections:
3V3: J2.5 (3V3), J3.2 (3V3), J3.5 (3V3), J3.8 (3V3), J4.1 (3V3), J4.19 (3V3)
BTN_NEXT: J2.19 (BTN_NEXT), SW1.1 (SIGNAL)
BTN_OK: J2.10 (BTN_OK), SW2.1 (SIGNAL)
CAM_D0: J1.4 (CAM_D0), J4.16 (CAM_D0)
CAM_D1: J1.5 (CAM_D1), J4.15 (CAM_D1)
CAM_D2: J1.6 (CAM_D2), J4.14 (CAM_D2)
CAM_D3: J1.7 (CAM_D3), J4.13 (CAM_D3)
CAM_D4: J1.9 (CAM_D4), J4.12 (CAM_D4)
CAM_D5: J1.10 (CAM_D5), J4.11 (CAM_D5)
CAM_D6: J1.11 (CAM_D6), J4.10 (CAM_D6)
CAM_D7: J1.12 (CAM_D7), J4.9 (CAM_D7)
CAM_HREF: J1.15 (CAM_HREF), J4.6 (CAM_HREF)
CAM_PCLK: J1.14 (CAM_PCLK), J4.7 (CAM_PCLK)
CAM_SCL: J1.20 (CAM_SCL), J4.3 (CAM_SCL)
CAM_SDA: J1.19 (CAM_SDA), J4.4 (CAM_SDA)
CAM_VSYNC: J1.16 (CAM_VSYNC), J4.5 (CAM_VSYNC)
CAM_XCLK: J2.14 (CAM_XCLK), J4.8 (CAM_XCLK)
GND: J1.3 (GND), J1.8 (GND), J1.13 (GND), J1.18 (GND), J2.3 (GND), J2.13 (GND), J2.18 (GND), J3.1 (GND), J3.7 (GND), J4.2 (GND), J4.20 (GND), J5.2 (GND), SW1.2 (GND), SW2.2 (GND)
LCD_DC: J2.20 (LCD_DC), J3.6 (LCD_DC)
LCD_MOSI: J2.16 (LCD_MOSI), J3.4 (LCD_MOSI)
LCD_SCK: J2.17 (LCD_SCK), J3.3 (LCD_SCK)
UART_TX: J1.1 (GP0_UART_TX), J5.1 (UART_TX)

Notes on the sheet:
Jitsu-in Pico 2 H carrier | connector-level schematic draft
Pico 2 H remains a socketed module. Verify connector orientation against the physical boards before PCB routing.
